ciprian-stingu/EpromProgrammer/gui/src/QtIcons.h

/**
 * 
 * Eprom Programmer
 * 
 * Copyright (C) 2021-2023 Ciprian Stingu
 * ciprian stingu at gmail dot com
 * 
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
 */
//----------------------------------------------------------------------
#ifndef QT_ICON_H
#define QT_ICON_H
//----------------------------------------------------------------------
/* XPM */
const char *guiIcon[]={
"256 256 852 2",
"Qt c None",
"#D c #000001",
".j c #000101",
".w c #010101",
".# c #010102",
".O c #010102",
"#l c #010103",
".i c #010202",
"h6 c #010203",
".a c #010304",
"id c #020305",
"ll c #020306",
"ib c #020405",
"lr c #020406",
".b c #020406",
".P c #020407",
"#S c #020507",
"a. c #030507",
".c c #030508",
"kJ c #030608",
".h c #030609",
".d c #030609",
".e c #04070a",
".f c #04070b",
".g c #04080c",
"ic c #04090c",
"#R c #05090d",
".6 c #05090d",
"#E c #05090e",
"#k c #050a0e",
"jq c #050a0f",
".x c #050a10",
"la c #060a10",
"cp c #060b10",
"l# c #060b10",
".Q c #060b11",
"kY c #060b12",
"il c #060c11",
"a# c #060c12",
"#9 c #070d13",
"#T c #070d14",
"lq c #070e15",
".k c #080e15",
"kG c #080e16",
"ct c #080f16",
".N c #080f16",
"d3 c #080f17",
"dr c #081017",
".v c #091018",
".5 c #091119",
"at c #0a131b",
"cq c #0a131c",
"#m c #0a131d",
"#C c #0a141d",
"cu c #0b151f",
"cs c #0c1722",
"aN c #0c1722",
".7 c #0d1723",
"cr c #0d1823",
"h9 c #0d1924",
"cg c #0d1925",
"js c #0d1a25",
"lp c #0d1a26",
"i# c #0e1a26",
".R c #0e1a27",
".l c #0e1b27",
".u c #0e1b28",
"#U c #0e1b29",
"co c #0f1c29",
"jl c #0f1d2a",
"bk c #0f1d2b",
"jt c #101e2c",
"lb c #101e2d",
"bN c #101f2d",
".y c #101f2e",
"bX c #10202f",
"aa c #11202f",
".4 c #11202f",
"b3 c #112130",
"#Q c #112130",
"#F c #122131",
"cJ c #122231",
"h7 c #122232",
".M c #122232",
"hR c #122333",
".m c #122333",
"hW c #122334",
".t c #122434",
"hV c #142638",
"kH c #142739",
"hX c #15293b",
"lm c #15293c",
"kX c #16293c",
".n c #15293d",
".8 c #16293d",
"hU c #162a3e",
"hH c #172b3f",
"hS c #172c40",
"hT c #172d42",
"lo c #182d42",
".o c #182e43",
"im c #193046",
"ln c #193147",
"au c #1a3147",
"ih c #1a3148",
".p c #1a3149",
"#n c #1a314a",
"cv c #1a3249",
"l. c #1a334a",
".q c #1a334b",
"kZ c #1b324b",
"ii c #1b334b",
".S c #1b334c",
".r c #1b344c",
".s c #1b344c",
"kA c #1b344d",
"#8 c #1c344d",
"lk c #1b354e",
"#V c #1c354e",
"ab c #1c354e",
".z c #1c364e",
"ig c #1c364f",
"if c #1c3650",
".L c #1d3852",
"kq c #1d3954",
"jo c #1e3954",
"kB c #1e3a55",
"jw c #1f3b57",
".9 c #1f3b57",
"jn c #1f3c57",
"kh c #1f3c58",
"a4 c #203c59",
"cK c #203d59",
"aO c #203d59",
"j9 c #203d5a",
"hy c #203e5b",
"jm c #213e5b",
"ek c #213f5c",
"it c #213f5d",
"#j c #21405d",
"d4 c #21405e",
"jj c #22415e",
"iu c #22415f",
"ho c #224260",
"ds c #234261",
"dK c #234362",
"ht c #234362",
"cQ c #244565",
"bj c #244565",
"lj c #244666",
"lc c #254666",
"a5 c #254667",
".A c #254767",
"cP c #254768",
".K c #254769",
"ij c #264869",
"cR c #26496a",
"cO c #26496b",
"#G c #26496c",
"#P c #264a6c",
"cN c #274b6e",
"j0 c #274c6e",
"bA c #274c6f",
"cL c #284c70",
"kz c #284c70",
"bl c #284d70",
"as c #284d71",
"k9 c #284e72",
"ac c #294d71",
"hI c #294e72",
".T c #294e72",
"cM c #294e73",
"av c #294f73",
"kQ c #294f75",
"ki c #295075",
"ch c #2a5075",
"#. c #295075",
"kr c #295076",
"bM c #295175",
".3 c #295176",
"#o c #2a5076",
"ia c #2a5176",
"i. c #2a5177",
"kK c #2a5277",
"bB c #2b5277",
"li c #2a5278",
"cb c #2b5278",
"ld c #2b5278",
"bW c #2b5378",
"#B c #2b5379",
".B c #2b5379",
".J c #2b537a",
"#i c #2b537a",
"bY c #2c547b",
"b9 c #2c547b",
"h8 c #2c557c",
"in c #2d567e",
"ju c #2d567e",
"ie c #2d577f",
"cS c #2e5881",
"jr c #2f5a83",
"kF c #2f5a85",
"#7 c #2f5b85",
"le c #2f5b85",
"#W c #305b85",
".C c #2f5b86",
".I c #2f5c87",
"hN c #305c87",
"cw c #305d88",
"hO c #315d89",
"kC c #305d89",
"hM c #315e89",
"kg c #315e8a",
"a3 c #325e8a",
"aP c #32608c",
"hL c #32618d",
"k8 c #32628f",
"lh c #33628e",
"hJ c #33628f",
"k0 c #33618f",
"lf c #33628f",
".D c #336290",
".U c #346390",
"kW c #336392",
".2 c #336492",
"aM c #346391",
"hY c #346492",
"aw c #346492",
"#p c #346493",
"## c #346493",
"kL c #346593",
"hK c #356593",
"kj c #346594",
"ir c #356594",
".E c #346595",
"lg c #346694",
"#h c #356695",
"iq c #356696",
"#A c #356797",
".F c #366797",
".G c #366797",
".H c #366898",
"ky c #366899",
"ad c #36699a",
"jx c #376a9b",
"ip c #386b9c",
"j8 c #376b9c",
"ks c #376b9d",
"bi c #376c9d",
"io c #386c9e",
"a6 c #396c9e",
"j1 c #396d9f",
"hz c #3a6fa2",
"#H c #3a6fa3",
"k7 c #3a70a3",
"#O c #3a70a4",
"#q c #3a70a4",
"kM c #3a70a5",
"el c #3b71a5",
".V c #3a71a5",
"hj c #3b71a5",
".1 c #3a72a6",
"kf c #3a71a6",
"#z c #3b71a6",
"jz c #3c72a7",
"d5 c #3c73a8",
"kV c #3a72a8",
"a2 c #3b72a8",
"kR c #3c72a8",
"aQ c #3c73a8",
"jk c #3c74a9",
"#a c #3c73a9",
"k. c #3c73aa",
"kp c #3b73aa",
"#g c #3b74aa",
"bz c #3c75aa",
"aL c #3c74ab",
"iv c #3d75ac",
"ax c #3c75ac",
"bm c #3e76ac",
"kk c #3c76ac",
"hp c #3e76ad",
"dt c #3e77ae",
"jy c #3e77af",
"d. c #3f78b0",
"kN c #3e78af",
"c9 c #3f79b0",
"#r c #3e78b0",
"c8 c #3f79b1",
"#y c #3e79b1",
"k6 c #407bb3",
"k1 c #3f7bb3",
".W c #407bb5",
"bL c #407cb4",
"is c #417cb5",
".0 c #407bb6",
"bC c #417cb6",
"#X c #417cb7",
"#6 c #417db7",
"j7 c #407db7",
"ke c #3f7db7",
"bh c #407db7",
"bV c #417eb8",
"kD c #417eb9",
"a1 c #407db8",
"bO c #427fba",
"k# c #407eb9",
"#b c #417eb9",
"#f c #417eba",
"a7 c #427fba",
"bZ c #437fbb",
"#s c #417eb9",
"#x c #417eba",
"b4 c #4380bb",
"c. c #4381bc",
"cx c #4381bd",
"ae c #4381be",
"c7 c #4482be",
"kt c #4381be",
"d# c #4482be",
"k5 c #4483be",
"hZ c #4483bf",
"ay c #4482bf",
"k2 c #4483bf",
"ik c #4483c0",
".X c #4483c1",
"kI c #4484c1",
"#I c #4583c1",
"jp c #4584c1",
"#N c #4484c2",
"cT c #4584c2",
"kO c #4282c0",
"jv c #4585c2",
"bg c #4282c0",
"#w c #4282c1",
"#t c #4382c1",
"hB c #4685c3",
"j2 c #4283c2",
"a8 c #4383c2",
"aR c #4484c3",
"hA c #4686c4",
"kU c #4484c3",
"hC c #4686c5",
"kS c #4385c3",
"by c #4486c3",
"da c #4687c5",
"dv c #4283c2",
"dQ c #4283c3",
"#c c #4484c4",
"a9 c #4485c4",
"du c #4686c5",
"k3 c #4687c5",
"k4 c #4787c5",
"#K c #4787c6",
"fD c #387dc0",
"fl c #397dc0",
"i0 c #397ec0",
"gL c #3a7ec1",
"e5 c #3b7fc1",
"fC c #3b7fc2",
"fk c #3b80c2",
"fu c #3b80c3",
"jg c #3c7fc1",
"iO c #3c80c1",
"jb c #3c80c2",
"fL c #3c80c3",
"d8 c #3c81c3",
"g0 c #3d80c2",
"d7 c #3d81c3",
"gw c #3d81c4",
"eM c #3e81c2",
"e4 c #3e81c3",
"jf c #3e82c3",
"dP c #3e82c4",
"ji c #3f82c2",
"dO c #3f82c4",
"d9 c #3f83c4",
"hc c #4082c3",
"f# c #4083c4",
"d6 c #4083c5",
"iP c #4084c5",
"#v c #4183c3",
"e6 c #4183c4",
"kP c #4184c3",
"jM c #4184c4",
"dN c #4184c5",
"bJ c #4284c3",
"#u c #4284c4",
"eL c #4284c5",
"jc c #4285c5",
"bn c #4384c4",
"bx c #4385c4",
"bo c #4385c5",
"e. c #4385c6",
"#d c #4485c5",
"kT c #4486c4",
"#e c #4486c5",
"dM c #4486c6",
"er c #4586c6",
"bK c #4587c5",
"bU c #4587c6",
"#M c #4687c6",
".Y c #4687c7",
"#L c #4688c7",
"#J c #4787c7",
".Z c #4788c7",
"ar c #4789c8",
"dL c #4888c7",
"af c #4888c8",
"eA c #4889c7",
"#Y c #4889c8",
"az c #4989c8",
"aK c #498ac8",
"#Z c #498ac9",
"em c #4a8ac8",
"ag c #4a8ac9",
"aq c #4a8bc9",
"jL c #4b8bc9",
"gZ c #4c8bc9",
"jA c #4c8cc9",
"#0 c #4c8cca",
"en c #4d8cc9",
"ko c #4d8dcb",
"ah c #4d8ecb",
"eq c #4e8dc9",
"jV c #4e8dca",
"bp c #4e8ecc",
"gK c #4f8dca",
"iZ c #4f8eca",
"bD c #4f8fcd",
"eo c #508eca",
"bP c #508fcd",
"#1 c #5090cd",
"ep c #518fca",
"hb c #518fcb",
"iw c #5290cb",
"jB c #5390cb",
"kd c #5392cf",
"aS c #5393cf",
"jE c #5491cc",
"ai c #5493cf",
"aA c #5494cf",
"iD c #5591cc",
"jh c #5592cc",
"#2 c #5593d0",
"jC c #5893cd",
"jD c #5894cd",
"#3 c #5896d2",
"g5 c #5994cd",
"eB c #5994ce",
"kE c #5997d3",
"#4 c #5a97d3",
"#5 c #5a98d4",
"ha c #5b96ce",
"b. c #5c9ad5",
"eK c #5d97cf",
"kn c #5d9bd6",
"aB c #5e9cd6",
"kc c #5e9cd7",
"aj c #5f9cd7",
"aT c #5f9dd7",
"gR c #6099d0",
"g6 c #6199d0",
"g9 c #619ad0",
"h# c #619ad1",
"h. c #629ad1",
"g8 c #629bd1",
"g7 c #639bd1",
"iE c #649cd1",
"bq c #65a1db",
"gY c #669ed2",
"jd c #679ed3",
"ix c #6aa0d4",
"bE c #6aa5de",
"kx c #6aa6df",
"eT c #6ba0d4",
"iA c #6ba1d4",
"ak c #6ba6df",
"bQ c #6ba7df",
"iC c #6ca1d4",
"iB c #6ca2d5",
"jZ c #6ca6df",
"aU c #6ca7df",
"b0 c #6ca7e0",
"iz c #6da2d5",
"b5 c #6da7e0",
"b8 c #6da8e0",
"km c #6da8e1",
"iy c #6ea2d5",
"jN c #6ea3d5",
"aC c #6ea9e1",
"b# c #6eaae1",
"eC c #6fa4d6",
"gx c #71a5d6",
"eJ c #73a6d7",
"ku c #73ade5",
"al c #74ade4",
"j# c #75a8d8",
"fV c #76a8d8",
"fa c #77a9d8",
"jF c #77a9d9",
"kv c #77b0e7",
"fM c #78a9d9",
"i9 c #78aad9",
"am c #78b0e7",
"kw c #78b1e8",
"fv c #79aad9",
"an c #79b1e8",
"ao c #79b2e8",
"ap c #79b2e9",
"gJ c #7babda",
"kb c #7bb3ea",
"ka c #7bb4ea",
"jK c #7cadda",
"aV c #7cb4ea",
"j6 c #7cb5eb",
"bf c #7db5eb",
"ba c #7db6eb",
"iY c #7eaedb",
"kl c #7fb7ec",
"eD c #80afdc",
"aD c #80b7ec",
"eH c #81b0dc",
"eG c #82b0dc",
"gc c #82b1dc",
"jY c #83b1dd",
"eI c #84b1dd",
"eF c #84b2dd",
"gq c #85b2dd",
"gj c #85b3dd",
"i1 c #85b3de",
"bI c #85bcf1",
"bF c #85bdf1",
"eE c #86b3de",
"iF c #88b4de",
"j5 c #88bef2",
"j3 c #88bff2",
"bb c #89bff2",
"bR c #89bff3",
"b1 c #8ac0f3",
"ca c #8ac0f4",
"b6 c #8ac1f4",
"c# c #8bc1f4",
"jG c #8cb7e0",
"aE c #8cc1f4",
"jJ c #8db8e0",
"bw c #8dc2f5",
"br c #8dc3f5",
"iN c #8eb9e1",
"je c #90bae1",
"jI c #91bae2",
"aF c #91c5f8",
"cm c #91c8fd",
"cl c #91c9fd",
"jH c #92bbe2",
"bc c #92c7f9",
"ck c #92c9fd",
"aG c #93c7f9",
"aH c #93c8fa",
"fE c #93c9fd",
"cj c #93cafd",
"aJ c #94c8fa",
"aI c #94c9fa",
"cn c #94cafd",
"ci c #95cafd",
"cf c #95cbfd",
"bv c #96cafc",
"bs c #96cbfc",
"ce c #96cbfd",
"eU c #97bfe4",
"aW c #97cafc",
"cd c #97cbfd",
"cc c #97ccfd",
"gS c #98bfe4",
"bt c #98ccfd",
"gV c #99c0e5",
"bd c #99ccfd",
"bH c #99cdfd",
"bu c #99cdfe",
"gX c #9ac1e5",
"dJ c #9acdfd",
"bT c #9acdfe",
"bS c #9acefe",
"bG c #9aceff",
"cy c #9bcdfd",
"dR c #9bcefd",
"b2 c #9bceff",
"b7 c #9bcfff",
"gW c #9cc2e6",
"cI c #9ccefd",
"aX c #9cceff",
"be c #9ccfff",
"j4 c #9cd0ff",
"gU c #9dc3e6",
"fF c #9dcefd",
"db c #9dcffd",
"aY c #9dd0ff",
"a0 c #9dd1ff",
"jO c #9ec4e7",
"es c #9ecffd",
"aZ c #9ed1ff",
"gT c #9fc4e7",
"e3 c #9fc5e7",
"cz c #9fcffd",
"ez c #9fd0fd",
"cH c #a0d0fd",
"cU c #a1d0fd",
"eN c #a1d1fd",
"cA c #a2d1fd",
"iG c #a3c7e8",
"dq c #a3d1fd",
"cG c #a3d2fd",
"gy c #a4c8e9",
"hi c #a4d2fd",
"iJ c #a5c8e9",
"cB c #a5d2fd",
"cF c #a5d3fd",
"iM c #a6c9e9",
"g1 c #a6d3fd",
"jU c #a7caea",
"cC c #a7d3fd",
"g4 c #a7d4fd",
"iK c #a8cbea",
"cD c #a8d4fd",
"iI c #a9cbeb",
"cE c #a9d4fd",
"et c #a9d5fd",
"iQ c #aacceb",
"dc c #aad5fd",
"iH c #abcdeb",
"h5 c #abd6fd",
"iL c #accdeb",
"d2 c #acd6fd",
"ey c #acd7fd",
"cV c #add6fd",
"hx c #add7fd",
"gI c #aecfec",
"eS c #aed7fd",
"h0 c #afd7fd",
"hq c #afd8fd",
"fW c #b0d0ed",
"hD c #b0d8fd",
"i7 c #b1d0ed",
"i5 c #b1d1ed",
"c6 c #b1d8fd",
"dp c #b1d9fd",
"fb c #b2d1ee",
"h1 c #b2d9fd",
"jW c #b3d2ee",
"dI c #b3d9fd",
"h4 c #b3d9fe",
"hd c #b3dafd",
"iX c #b4d3ee",
"fN c #b4d3ef",
"gr c #b4dafd",
"j. c #b5d3ef",
"e# c #b5dafd",
"h2 c #b5dafe",
"g2 c #b5dbfd",
"gm c #b6d4ef",
"hQ c #b6dbfd",
"fG c #b6dbfe",
"ge c #b7d5f0",
"ft c #b7dbfd",
"h3 c #b7dbfe",
"hu c #b7dcfd",
"fw c #b8d5f0",
"cW c #b8dcfd",
"gk c #b8dcfe",
"eV c #b9d6f0",
"gv c #b9dcfd",
"dS c #b9dcfe",
"hw c #b9ddfd",
"fR c #baddfe",
"ej c #badefe",
"eZ c #bbd7f1",
"eY c #bbd8f1",
"c5 c #bbddfd",
"i6 c #bcd8f1",
"dw c #bcdefd",
"gd c #bcdefe",
"e2 c #bdd9f2",
"dd c #bddefd",
"fK c #bddefe",
"fZ c #bddffe",
"jX c #bedaf2",
"eR c #bedffd",
"f7 c #bedffe",
"e0 c #bfdaf3",
"d1 c #bfdffe",
"cX c #c0e0fe",
"eX c #c1dbf3",
"gp c #c1dcf3",
"f. c #c1e0fd",
"fU c #c1e0fe",
"i4 c #c2dcf3",
"c4 c #c2e1fe",
"eW c #c3ddf4",
"dH c #c3e1fd",
"eu c #c3e1fe",
"do c #c3e2fd",
"e1 c #c4ddf4",
"f2 c #c4e2fe",
"jR c #c5def5",
"g. c #c5e2fe",
"jQ c #c6dff5",
"cY c #c6e3fe",
"jT c #c7e0f5",
"hs c #c7e3fe",
"gQ c #c7e4fe",
"c3 c #c8e3fe",
"ex c #c8e4fe",
"hv c #c9e4fe",
"jS c #cae2f6",
"dT c #cae4fe",
"jP c #cbe2f7",
"cZ c #cbe5fe",
"he c #cbe6fe",
"gz c #cce3f7",
"c2 c #cce5fe",
"hP c #cde6fe",
"gD c #cee4f8",
"gE c #cee5f8",
"c0 c #cee6fe",
"hh c #cee7fe",
"gC c #cfe5f8",
"c1 c #cfe7fe",
"gH c #d0e6f9",
"fs c #d0e8fe",
"ea c #d1e8fe",
"eO c #d2e8fe",
"gF c #d3e8fa",
"e9 c #d3e9fe",
"dn c #d3eafe",
"iR c #d4e8fa",
"gu c #d4eafe",
"gB c #d5e9fa",
"dG c #d5eafe",
"iV c #d6eafb",
"eQ c #d6ebfe",
"iU c #d7eafb",
"dU c #d7ebfe",
"ei c #d7ecfe",
"gA c #d8ebfb",
"gG c #d8ebfc",
"gM c #d8ecfe",
"gl c #d9ecfe",
"gP c #d9edfe",
"ja c #daecfc",
"hG c #daecfe",
"g3 c #daedfe",
"fJ c #dbedfe",
"de c #dcedfe",
"fX c #dceefd",
"d0 c #dceefe",
"fS c #ddeefe",
"iT c #ddeffd",
"dm c #deeffe",
"hn c #dfeffe",
"fc c #dff0fe",
"fm c #e0effe",
"dx c #e0f0fe",
"i8 c #e0f1fe",
"iS c #e0f1ff",
"e7 c #e1f0fe",
"iW c #e1f1ff",
"fg c #e1f2ff",
"ev c #e2f0fe",
"fT c #e2f1fe",
"f0 c #e2f1ff",
"ff c #e2f2ff",
"fr c #e3f1fe",
"f8 c #e3f2ff",
"fj c #e3f3ff",
"dV c #e4f1fe",
"dF c #e4f2fe",
"gb c #e4f3ff",
"df c #e5f2fe",
"f4 c #e5f2ff",
"f6 c #e5f3ff",
"fQ c #e5f4ff",
"gs c #e6f3fe",
"fP c #e6f4ff",
"f3 c #e6f5ff",
"dl c #e7f3fe",
"dZ c #e7f4fe",
"ew c #e7f4ff",
"fY c #e7f5ff",
"fh c #e7f6ff",
"eb c #e8f3ff",
"gN c #e8f4fe",
"hf c #e8f4ff",
"ga c #e8f6ff",
"gO c #e9f4fe",
"f9 c #e9f4ff",
"fe c #e9f7ff",
"gg c #eaf7ff",
"fA c #eaf8ff",
"f5 c #ebf5ff",
"fz c #ebf8ff",
"gi c #ebf9ff",
"fH c #ecf5fe",
"dg c #ecf5ff",
"eh c #ecf6ff",
"fd c #ecf9ff",
"dy c #edf6fe",
"dk c #edf6ff",
"fi c #edf9ff",
"g# c #edfaff",
"fn c #eef6fe",
"hr c #eef6ff",
"dW c #eef7fe",
"go c #eefaff",
"hF c #eff7ff",
"gh c #effbff",
"fq c #f0f7fe",
"dE c #f0f8fe",
"eP c #f0f8ff",
"i3 c #f0fbff",
"fO c #f0fcff",
"dh c #f1f7ff",
"dj c #f1f8ff",
"hk c #f1f9ff",
"fB c #f1fcff",
"di c #f2f8ff",
"e8 c #f2f9ff",
"fy c #f2fdff",
"ec c #f3f9ff",
"gn c #f3feff",
"hm c #f4f9ff",
"i2 c #f4feff",
"eg c #f5faff",
"gf c #f5ffff",
"hE c #f6faff",
"fx c #f6ffff",
"dz c #f7faff",
"dX c #f7fbff",
"fo c #f8fbff",
"dD c #f8fcff",
"fp c #f9fcff",
"ed c #fafcff",
"ef c #fafdff",
"gt c #fbfdff",
"f1 c #fbfeff",
"hl c #fcfdff",
"fI c #fcfeff",
"dY c #fdfeff",
"hg c #fdffff",
"dA c #fefeff",
"ee c #feffff",
"dC c #fffeff",
"dB c #ffffff",
"QtQtQtQtQtQtQtQtQtQtQtQtQtQtQtQtQtQtQtQtQtQtQtQtQtQtQtQtQtQtQtQtQtQtQtQtQtQtQtQtQtQtQtQtQtQtQtQtQtQtQtQtQtQtQtQtQtQtQtQtQtQtQtQtQtQtQtQtQtQtQtQtQtQtQtQtQtQtQtQtQtQtQtQtQtQtQtQtQtQtQtQtQtQtQtQtQtQtQtQtQtQtQtQtQtQtQtQtQtQtQtQtQtQtQtQtQtQtQtQtQtQtQtQtQtQtQtQtQtQtQtQtQtQtQtQtQtQtQtQtQtQtQtQtQtQtQtQtQtQtQtQtQtQtQtQtQtQtQtQtQtQtQtQtQtQtQtQtQtQtQtQtQtQtQtQtQtQtQtQtQtQtQtQtQtQtQtQtQtQtQtQtQtQtQtQtQtQtQtQtQtQtQtQtQtQtQtQtQtQtQtQtQtQtQtQtQtQtQtQtQtQtQtQtQtQtQtQtQtQtQtQtQtQtQtQtQtQtQtQtQtQtQtQtQtQtQtQtQtQtQtQtQtQtQtQt",
"QtQtQtQtQtQtQtQtQtQtQtQtQtQtQtQtQtQtQtQtQtQtQtQtQtQtQtQtQtQtQtQtQtQtQtQtQtQtQtQtQtQtQtQtQtQtQtQtQtQtQtQtQtQtQtQtQtQtQtQtQtQtQtQtQtQtQtQtQtQtQtQtQtQtQtQtQtQtQtQtQtQtQtQtQtQtQtQtQtQtQtQtQtQtQtQtQtQtQtQtQtQtQtQtQtQtQtQtQtQtQtQtQtQtQtQtQtQtQtQtQtQtQtQtQtQtQtQtQtQtQtQtQtQtQtQtQtQtQtQtQtQtQtQtQtQtQtQtQtQtQtQtQtQtQtQtQtQtQtQtQtQtQtQtQtQtQtQtQtQtQtQtQtQtQtQtQtQtQtQtQtQtQtQtQtQtQtQtQtQtQtQtQtQtQtQtQtQtQtQtQtQtQtQtQtQtQtQtQtQtQtQtQtQtQtQtQtQtQtQtQtQtQtQtQtQtQtQtQtQtQtQtQtQtQtQtQtQtQtQtQtQtQtQtQtQtQtQtQtQtQtQtQtQtQtQt",
"QtQtQtQtQtQtQtQtQtQtQtQtQtQtQtQtQtQtQtQtQtQtQtQtQtQtQtQtQtQtQtQtQtQtQtQtQtQtQtQtQtQtQtQtQtQtQtQtQtQtQtQtQtQtQtQtQtQtQtQtQtQtQtQtQtQtQtQtQtQtQtQtQtQtQtQtQtQtQtQtQtQtQtQtQtQtQtQtQtQtQtQtQtQtQtQtQtQtQtQtQtQtQtQtQtQtQtQtQtQtQtQtQtQtQtQtQtQtQtQtQtQtQtQtQtQtQtQtQtQtQtQtQtQtQtQtQtQtQtQtQtQtQtQtQtQtQtQtQtQtQtQtQtQtQtQtQtQtQtQtQtQtQtQtQtQtQtQtQtQtQtQtQtQtQtQtQtQtQtQtQtQtQtQtQtQtQtQtQtQtQtQtQtQtQtQtQtQtQtQtQtQtQtQtQtQtQtQtQtQtQtQtQtQtQtQtQtQtQtQtQtQtQtQtQtQtQtQtQtQtQtQtQtQtQtQtQtQtQtQtQtQtQtQtQtQtQtQtQtQtQtQtQtQtQtQt",
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
"QtQtQtQtQtQtQtQtQtQtQtQtQtQtQtQtQtQtQtQtQtQt.j.jQtQtQtQtQtQtQtQtQtQtQtQtQtQtQtQtQtQtQtQtQtQtQtQtQtQtcobBbZ#M#ubn#1b0cab7aZbGbtbtbtbtbtbtbtbtbtbtbtbtbtbtbtbtbtbtbtbtcccececfcicncncncncncicicfcecdccbtbtbtbtbtbtbtbtbtbtbtbtbtbtbtbtbtbtbtbtbtbtbtbtbtbtbtbtbtbtbtbtbtbtbtbtbtbtbtbtbtbtbtbtbtbtbtbtbtbtbtbtbtbtbtbtbtbtbtbtbtbtbtbtbtbtbtbtbtbtbtbtbtbtbtbtbtbtbtbtbtbtbtbtbtbtbtbtbtbtbtbtbtbtbtbtbGaZb7cab0#1bn#u#MbZbBcoQtQtQtQtQtQtQtQtQtQtQtQtQtQtQtQtQtQtQtQtQtQtQtQtQtQt.j.jQtQtQtQtQtQtQtQtQtQtQtQtQtQtQtQtQtQtQtQtQtQt",
"QtQtQtQtQtQtQtQtQtQtQtQtQtQtQtQtQtQtQtQtQtQtQtQt.acpcqcrcgcraNaNaNaNaNaNaNaNaNaNaNaNaNaNaNaNcsatctcucvcwcx#M#ubn#1b0cab7aZbGbtbtbtbtbtbtbtbtbtbtbtbtbtbtbtbtbtbtccbtcyczcAcBcCcDcEcEcEcDcCcFcGcHcIbHbtbtbtbtbtbtbtbtbtbtbtbtbtbtbtbtbtbtbtbtbtbtbtbtbtbtbtbtbtbtbtbtbtbtbtbtbtbtbtbtbtbtbtbtbtbtbtbtbtbtbtbtbtbtbtbtbtbtbtbtbtbtbtbtbtbtbtbtbtbtbtbtbtbtbtbtbtbtbtbtbtbtbtbtbtbtbtbtbtbtbtbtbtbtbtbtbGaZb7cab0#1bn#u#McxcwcvcuctatcsaNaNaNaNaNaNaNaNaNaNaNaNaNaNaNaNcrcgcrcqcp.aQtQtQtQtQtQtQtQtQtQtQtQtQtQtQtQtQtQtQtQtQtQtQtQt",
"QtQtQtQtQtQtQtQtQtQtQtQtQtQtQtQtQtQtQtQtQtQtQtQt.gcJcKcLcMcNcOcOcOcOcOcOcOcOcOcOcOcOcOcOcOcOcOcPcQcRcS#OcT#M#ubn#1b0cab7aZbGbtbtbtbtbtbtbtbtbtbtbtbtbtbtbtcccccecebtcUcVcWcXcYcZc0c1c0c2c3c4c5c6cBcIbtccccccccbtbtbtbtbtbtbtbtbtbtbtbtbtbtbtbtbtbtbtbtbtbtbtbtbtbtbtbtbtbtbtbtbtbtbtbtbtbtbtbtbtbtbtbtbtbtbtbtbtbtbtbtbtbtbtbtbtbtbtbtbtbtbtbtbtbtbtbtbtbtbtbtbtbtbtbtbtbtbtbtbtbtbtbtbtbtbtbtbtbtbtbGaZb7cab0#1bn#u#McT#OcScRcQcPcOcOcOcOcOcOcOcOcOcOcOcOcOcOcOcOcOcNcMcLcKcJ.gQtQtQtQtQtQtQtQtQtQtQtQtQtQtQtQtQtQtQtQtQtQtQtQt",
"QtQtQtQtQtQtQtQtQtQtQtQtQtQtQtQtQtQtQtQtQtQtQtQt#T.L#p#6c7bCc8c8c8c8c8c8c8c8c8c8c8c8c8c8c8c8c8c9d.c9bCd#dabUbJbn#1b0cab7aZbGbtbtbtbtbtbtbtbtbtbtbtbtbtbtcccdccccbtdbdcddc1dedfdgdhdidjdkdldmdndodpdqcIbdbtcdccbtbtbtbtbtbtbtbtbtbtbtbtbtbtbtbtbtbtbtbtbtbtbtbtbtbtbtbtbtbtbtbtbtbtbtbtbtbtbtbtbtbtbtbtbtbtbtbtbtbtbtbtbtbtbtbtbtbtbtbtbtbtbtbtbtbtbtbtbtbtbtbtbtbtbtbtbtbtbtbtbtbtbtbtbtbtbtbtbtbtbtbGaZb7cab0#1bnbJbUdad#bCc9d.c9c8c8c8c8c8c8c8c8c8c8c8c8c8c8c8c8c8bCc7#6#p.L#TQtQtQtQtQtQtQtQtQtQtQtQtQtQtQtQtQtQtQtQtQtQtQtQt",
"QtQtQtQtQtQtQtQtQtQtQtQtQtQtQtQtQtQtQtQtQtQtQtQtdrdsdt.Z.Z.Z.Z.Z.Y#MbUbU#M#M#M#M#M#M#M#M#M#M#MbUbUbU.Y#L.Zdudvbn#1b0cab7aZbGbtbtbtbtbtbtbtbtbtbtbtbtbtbtccccbHdbcGcVdwc1dxdydzdAdBdBdBdCdDdEdFdGdHdIcDcHdJcdcdbtbtbtbtbtbtbtbtbtbtbtbtbtbtbtbtbtbtbtbtbtbtbtbtbtbtbtbtbtbtbtbtbtbtbtbtbtbtbtbtbtbtbtbtbtbtbtbtbtbtbtbtbtbtbtbtbtbtbtbtbtbtbtbtbtbtbtbtbtbtbtbtbtbtbtbtbtbtbtbtbtbtbtbtbtbtbtbtbtbtbtbGaZb7cab0#1bndvdu.Z#L.YbUbUbU#M#M#M#M#M#M#M#M#M#M#MbUbU#M.Y.Z.Z.Z.Z.ZdtdsdrQtQtQtQtQtQtQtQtQtQtQtQtQtQtQtQtQtQtQtQtQtQtQtQt",
"QtQtQtQtQtQtQtQtQtQtQtQtQtQtQtQtQtQtQtQtQtQtQtQtdrdKd..Z.ZdL.ZdMdNdOdPdPdOdOdOdOdOdOdOdOdOdOdOdPdPdOdNdM#LdudQbn#1b0cab7aZbGbtbtbtbtbtbtbtbtbtbtbtbtbtbtcecedRcDdSdTdUdVdWdXdYdBdBdBdBdBdAdDdjdZd0c1d1d2dbcecebtbtbtbtbtbtbtbtbtbtbtbtbtbtbtbtbtbtbtbtbtbtbtbtbtbtbtbtbtbtbtbtbtbtbtbtbtbtbtbtbtbtbtbtbtbtbtbtbtbtbtbtbtbtbtbtbtbtbtbtbtbtbtbtbtbtbtbtbtbtbtbtbtbtbtbtbtbtbtbtbtbtbtbtbtbtbtbtbtbtbtbGaZb7cab0#1bndQdu#LdMdNdOdPdPdOdOdOdOdOdOdOdOdOdOdOdPdPdOdNdM.ZdL.Z.Zd.dKdrQtQtQtQtQtQtQtQtQtQtQtQtQtQtQtQtQtQtQtQtQtQtQtQt",
"QtQtQtQtQtQtQtQtQtQtQtQtQtQtQtQtQtQtQtQtQtQtQtQtd3d4d5.Z.ZdL.ZdMd6d7d8d7d7d7d7d7d7d7d7d7d7d7d7d7d8d7d9e.#L#M#ubn#1b0cab7aZbGbtbtbtbtbtbtbtbtbtbtbtbtbtbtcdcccHe#eaebecdXeddYeedBdBdBdBdBdBdYefdDegeheiejcAcccebtbtbtbtbtbtbtbtbtbtbtbtbtbtbtbtbtbtbtbtbtbtbtbtbtbtbtbtbtbtbtbtbtbtbtbtbtbtbtbtbtbtbtbtbtbtbtbtbtbtbtbtbtbtbtbtbtbtbtbtbtbtbtbtbtbtbtbtbtbtbtbtbtbtbtbtbtbtbtbtbtbtbtbtbtbtbtbtbtbtbtbGaZb7cab0#1bn#u#M#Le.d9d7d8d7d7d7d7d7d7d7d7d7d7d7d7d7d8d7d6dM.ZdL.Z.Zd5d4d3QtQtQtQtQtQtQtQtQtQtQtQtQtQtQtQtQtQtQtQtQtQtQtQt",
"QtQtQtQtQtQtQtQtQtQtQtQtQtQtQtQtQtQtQtQtQtQtQtQtctekel.Z.Z#L.ZemeneoepeoeoeoeoeoeoeoeoeoeoeoeoeoepeoeqemdLer#v#u#1b0cab7aZbGbtbtbtbtbtbtbtbtbtbtbtcccdbddJeseteueveddBdBdBdBdBdBdBdBdBdBdBdBdBdBdBdYewexeyezdJbdcccdbtbtbtbtbtbtbtbtbtbtbtbtbtbtbtbtbtbtbtbtbtbtbtbtbtbtbtbtbtbtbtbtbtbtbtbtbtbtbtbtbtbtbtbtbtbtbtbtbtbtbtbtbtbtbtbtbtbtbtbtbtbtbtbtbtbtbtbtbtbtbtbtbtbtbtbtbtbtbtbtbtbtbtbtbtbtbtbtbGaZb7cab0#1#u#verdLemeqeoepeoeoeoeoeoeoeoeoeoeoeoeoeoepeoenem.Z#L.Z.ZelekctQtQtQtQtQtQtQtQtQtQtQtQtQtQtQtQtQtQtQtQtQtQtQtQt",
"QtQtQtQtQtQtQtQtQtQtQtQtQtQtQtQtQtQtQtQtQtQtQtQtctekel.ZdMe.eAeBeCeDeEeFeGeHeHeHeHeHeHeHeHeHeHeIeEeGeJeKemeLeM#u#1b0cab7aZbGbtbtbtbtbtbtbtbtbtbtbtcecedJeNd2c5eOdgdBdBdBdBdBdBdBdBdBdBdBdBdBdBdBdBdBePeQeReScGcycececcbtbtbtbtbtbtbtbtbtbtbtbtbtbtbtbtbtbtbtbtbtbtbtbtbtbtbtbtbtbtbtbtbtbtbtbtbtbtbtbtbtbtbtbtbtbtbtbtbtbtbtbtbtbtbtbtbtbtbtbtbtbtbtbtbtbtbtbtbtbtbtbtbtbtbtbtbtbtbtbtbtbtbtbtbtbtbtbGaZb7cab0#1#ueMeLemeKeJeGeEeIeHeHeHeHeHeHeHeHeHeHeGeFeEeDeCeBeAe.dM.ZelekctQtQtQtQtQtQtQtQtQtQtQtQtQtQtQtQtQtQtQtQtQtQtQtQt",
"QtQtQtQtQtQtQtQtQtQtQtQtQtQtQtQtQtQtQtQtQtQtQtQtctekel.ZeLdOazeTeUeVeWeXeYeZeZeZeZeZeZeZeZeZeZe0e1e2e3eJeqe4e5e6#1b0cab7aZbGbtbtbtbtbtbtbtbtbtbtcccicncydcddc1e7e8dBdBdBdBdBdBdBdBdBdBdBdBdBdBdBdBdBegdfe9f.eSdbcfcnccbtbtbtbtbtbtbtbtbtbtbtbtbtbtbtbtbtbtbtbtbtbtbtbtbtbtbtbtbtbtbtbtbtbtbtbtbtbtbtbtbtbtbtbtbtbtbtbtbtbtbtbtbtbtbtbtbtbtbtbtbtbtbtbtbtbtbtbtbtbtbtbtbtbtbtbtbtbtbtbtbtbtbtbtbtbtbtbGaZb7cab0#1e6e5e4eqeJe3e2e1e0eZeZeZeZeZeZeZeZeZeZeYeXeWeVeUeTazdOeL.ZelekctQtQtQtQtQtQtQtQtQtQtQtQtQtQtQtQtQtQtQtQtQtQtQtQt",
"QtQtQtQtQtQtQtQtQtQtQtQtQtQtQtQtQtQtQtQtQtQtQtQtctekel#Lf#d8emfafbfcfdfefffgfgfgfgfgfgfgfgfgfgfhfifje2eGeofkfl#v#1b0cab7aZbGbtbtbtbtbtbtbtbtbtbtcccncjcIc6cZfmfnfodBdBdBdBdBdBdBdBdBdBdBdBdBdBdBdBdBfpfqfrfsftezcncjcdbtbtbtbtbtbtbtbtbtbtbtbtbtbtbtbtbtbtbtbtbtbtbtbtbtbtbtbtbtbtbtbtbtbtbtbtbtbtbtbtbtbtbtbtbtbtbtbtbtbtbtbtbtbtbtbtbtbtbtbtbtbtbtbtbtbtbtbtbtbtbtbtbtbtbtbtbtbtbtbtbtbtbtbtbtbtbtbGaZb7cab0#1#vflfkeoeGe2fjfifhfgfgfgfgfgfgfgfgfgfgfffefdfcfbfaemd8f##LelekctQtQtQtQtQtQtQtQtQtQtQtQtQtQtQtQtQtQtQtQtQtQtQtQt",
"QtQtQtQtQtQtQtQtQtQtQtQtQtQtQtQtQtQtQtQtQtQtQtQtctekel#Lf#fuemfvfwfhfxfyfzfAfAfAfAfAfAfAfAfAfAfBfxfie1eEepfCfD#v#1b0cab7aZbGbtbtbtbtbtbtbtbtbtbtcccjfEfFfGdGfHdXfIdBdBdBdBdBdBdBdBdBdBdBdBdBdBdBdBdBdYfodWfJfKcUcjfEcebtbtbtbtbtbtbtbtbtbtbtbtbtbtbtbtbtbtbtbtbtbtbtbtbtbtbtbtbtbtbtbtbtbtbtbtbtbtbtbtbtbtbtbtbtbtbtbtbtbtbtbtbtbtbtbtbtbtbtbtbtbtbtbtbtbtbtbtbtbtbtbtbtbtbtbtbtbtbtbtbtbtbtbtbtbtbtbGaZb7cab0#1#vfDfCepeEe1fifxfBfAfAfAfAfAfAfAfAfAfAfzfyfxfhfwfvemfuf##LelekctQtQtQtQtQtQtQtQtQtQtQtQtQtQtQtQtQtQtQtQtQtQtQtQt",
"QtQtQtQtQtQtQtQtQtQtQtQtQtQtQtQtQtQtQtQtQtQtQtQtctekel#Lf#fLemfMfNfffOfifPfQfQfQfQfQfQfQfQfQfQfzfBfhe0eIeofkfD#v#1b0cab7aZbGbtbtbtbtbtbtbtbtbtbtccfEckdbfRfSegeedBdBdBdBdBdBdBdBdBdBdBdBdBdBdBdBdBdBdBdAdXfTfUcAcjckcebtbtbtbtbtbtbtbtbtbtbtbtbtbtbtbtbtbtbtbtbtbtbtbtbtbtbtbtbtbtbtbtbtbtbtbtbtbtbtbtbtbtbtbtbtbtbtbtbtbtbtbtbtbtbtbtbtbtbtbtbtbtbtbtbtbtbtbtbtbtbtbtbtbtbtbtbtbtbtbtbtbtbtbtbtbtbtbGaZb7cab0#1#vfDfkeoeIe0fhfBfzfQfQfQfQfQfQfQfQfQfQfPfifOfffNfMemfLf##LelekctQtQtQtQtQtQtQtQtQtQtQtQtQtQtQtQtQtQtQtQtQtQtQtQt",
"QtQtQtQtQtQtQtQtQtQtQtQtQtQtQtQtQtQtQtQtQtQtQtQtctekel#Lf#d8emfVfWfXfAfYdxfcfcfcfcfcfcfcfcfcfcfQfAfgeZeHeofkfl#v#1b0cab7aZbGbtbtbtbtbtbtbtbtbtbtcdckclesfZf0f1dBdBdBdBdBdBdBdBdBdBdBdBdBdBdBdBdBdBdBdBdBdYebf2dqfEckcebtbtbtbtbtbtbtbtbtbtbtbtbtbtbtbtbtbtbtbtbtbtbtbtbtbtbtbtbtbtbtbtbtbtbtbtbtbtbtbtbtbtbtbtbtbtbtbtbtbtbtbtbtbtbtbtbtbtbtbtbtbtbtbtbtbtbtbtbtbtbtbtbtbtbtbtbtbtbtbtbtbtbtbtbtbtbtbGaZb7cab0#1#vflfkeoeHeZfgfAfQfcfcfcfcfcfcfcfcfcfcdxfYfAfXfWfVemd8f##LelekctQtQtQtQtQtQtQtQtQtQtQtQtQtQtQtQtQtQtQtQtQtQtQtQt",
"QtQtQtQtQtQtQtQtQtQtQtQtQtQtQtQtQtQtQtQtQtQtQtQtctekel#Lf#d8emfVfWfXfAf3dxfcfcfcfcfcfcfcfcfcfcfQfAfgeZeHeofkfl#v#1b0cab7aZbGbtbtbtbtbtbtbtbtbtbtcdckclesd1f4eedBdBdBdBdBdBdBdBdBdBdBdBdBdBdBdBdBdBdBdBdBdBf5cYdqckclcebtbtbtbtbtbtbtbtbtbtbtbtbtbtbtbtbtbtbtbtbtbtbtbtbtbtbtbtbtbtbtbtbtbtbtbtbtbtbtbtbtbtbtbtbtbtbtbtbtbtbtbtbtbtbtbtbtbtbtbtbtbtbtbtbtbtbtbtbtbtbtbtbtbtbtbtbtbtbtbtbtbtbtbtbtbtbtbGaZb7cab0#1#vflfkeoeHeZfgfAfQfcfcfcfcfcfcfcfcfcfcdxf3fAfXfWfVemd8f##LelekctQtQtQtQtQtQtQtQtQtQtQtQtQtQtQtQtQtQtQtQtQtQtQtQt",
"QtQtQtQtQtQtQtQtQtQtQtQtQtQtQtQtQtQtQtQtQtQtQtQtctekel#Lf#d8emfVfWfXfAf3dxfcfcfcfcfcfcfcfcfcfcfQfAfgeZeHeofkfl#v#1b0cab7aZbGbtbtbtbtbtbtbtbtbtbtcdckclesd1f6dBdBdBdBdBdBdBdBdBdBdBdBdBdBdBdBdBdBdBdBdBdBdBf5cYdqckclcebtbtbtbtbtbtbtbtbtbtbtbtbtbtbtbtbtbtbtbtbtbtbtbtbtbtbtbtbtbtbtbtbtbtbtbtbtbtbtbtbtbtbtbtbtbtbtbtbtbtbtbtbtbtbtbtbtbtbtbtbtbtbtbtbtbtbtbtbtbtbtbtbtbtbtbtbtbtbtbtbtbtbtbtbtbtbtbGaZb7cab0#1#vflfkeoeHeZfgfAfQfcfcfcfcfcfcfcfcfcfcdxf3fAfXfWfVemd8f##LelekctQtQtQtQtQtQtQtQtQtQtQtQtQtQtQtQtQtQtQtQtQtQtQtQt",
"QtQtQtQtQtQtQtQtQtQtQtQtQtQtQtQtQtQtQtQtQtQtQtQtctekel#Lf#d8emfVfWfXfAf3dxfcfcfcfcfcfcfcfcfcfcfQfAfgeZeHeofkfl#v#1b0cab7aZbGbtbtbtbtbtbtbtbtbtbtcdckclesf7f8dYdBdBdBdBdBdBdBdBdBdBdBdBdBdBdBdBdBdBdBdBdBeef9g.dqfEckcebtbtbtbtbtbtbtbtbtbtbtbtbtbtbtbtbtbtbtbtbtbtbtbtbtbtbtbtbtbtbtbtbtbtbtbtbtbtbtbtbtbtbtbtbtbtbtbtbtbtbtbtbtbtbtbtbtbtbtbtbtbtbtbtbtbtbtbtbtbtbtbtbtbtbtbtbtbtbtbtbtbtbtbtbtbtbtbGaZb7cab0#1#vflfkeoeHeZfgfAfQfcfcfcfcfcfcfcfcfcfcdxf3fAfXfWfVemd8f##LelekctQtQtQtQtQtQtQtQtQtQtQtQtQtQtQtQtQtQtQtQtQtQtQtQt",
"QtQtQtQtQtQtQtQtQtQtQtQtQtQtQtQtQtQtQtQtQtQtQtQtctekel#Lf#d8emfafbfcg#feffffffffffffffffffffffgag#gbe2gceofkfl#v#1b0cab7aZbGbtbtbtbtbtbtbtbtbtbtccfEckesgdfcdDdBdBdBdBdBdBdBdBdBdBdBdBdBdBdBdBdBdBdBdBdBfpf4c4cAfEckcebtbtbtbtbtbtbtbtbtbtbtbtbtbtbtbtbtbtbtbtbtbtbtbtbtbtbtbtbtbtbtbtbtbtbtbtbtbtbtbtbtbtbtbtbtbtbtbtbtbtbtbtbtbtbtbtbtbtbtbtbtbtbtbtbtbtbtbtbtbtbtbtbtbtbtbtbtbtbtbtbtbtbtbtbtbtbtbGaZb7cab0#1#vflfkeogce2gbg#gafffffffffffffffffffffffeg#fcfbfaemd8f##LelekctQtQtQtQtQtQtQtQtQtQtQtQtQtQtQtQtQtQtQtQtQtQtQtQt",
"QtQtQtQtQtQtQtQtQtQtQtQtQtQtQtQtQtQtQtQtQtQtQtQtctekel#Lf#fLemfvgef3gffBggfefefefefefefefefefeghgfgieWgjepfCfD#v#1b0cab7aZbGbtbtbtbtbtbtbtbtbtbtccfEckdbgkglePefdAdBdBdBdBdBdBdBdBdBdBdBdBdBdBdBdBdBdAefdifSf7eNcjckcebtbtbtbtbtbtbtbtbtbtbtbtbtbtbtbtbtbtbtbtbtbtbtbtbtbtbtbtbtbtbtbtbtbtbtbtbtbtbtbtbtbtbtbtbtbtbtbtbtbtbtbtbtbtbtbtbtbtbtbtbtbtbtbtbtbtbtbtbtbtbtbtbtbtbtbtbtbtbtbtbtbtbtbtbtbtbtbGaZb7cab0#1#vfDfCepgjeWgigfghfefefefefefefefefefeggfBgff3gefvemfLf##LelekctQtQtQtQtQtQtQtQtQtQtQtQtQtQtQtQtQtQtQtQtQtQtQtQt",
"QtQtQtQtQtQtQtQtQtQtQtQtQtQtQtQtQtQtQtQtQtQtQtQtctekel#Lf#fLemfvgmfQgnghgafhfhfhfhfhfhfhfhfhgagogngggpgqepfCfD#v#1b0cab7aZbGbtbtbtbtbtbtbtbtbtbtcccnfEcIgrfsgse8efdBdBdBdBdBdBdBdBdBdBdBdBdBdBdBdBdBgtecdlgugvcHcncjcdbtbtbtbtbtbtbtbtbtbtbtbtbtbtbtbtbtbtbtbtbtbtbtbtbtbtbtbtbtbtbtbtbtbtbtbtbtbtbtbtbtbtbtbtbtbtbtbtbtbtbtbtbtbtbtbtbtbtbtbtbtbtbtbtbtbtbtbtbtbtbtbtbtbtbtbtbtbtbtbtbtbtbtbtbtbtbtbGaZb7cab0#1#vfDfCepgqgpgggngogafhfhfhfhfhfhfhfhfhgaghgnfQgmfvemfLf##LelekctQtQtQtQtQtQtQtQtQtQtQtQtQtQtQtQtQtQtQtQtQtQtQtQt",
"QtQtQtQtQtQtQtQtQtQtQtQtQtQtQtQtQtQtQtQtQtQtQtQtctekel#LdNgwaKgxgygzgAgBgCgDgDgDgDgDgDgDgDgDgEgFgGgHgIgJgKd8gL#v#1b0cab7aZbGbtbtbtbtbtbtbtbtbtbtcccncncIeSg.gMgNegeedBdBdBdBdBdBdBdBdBdBdBdBdBdBdBdBdXgOgPgQdpescicncdbtbtbtbtbtbtbtbtbtbtbtbtbtbtbtbtbtbtbtbtbtbtbtbtbtbtbtbtbtbtbtbtbtbtbtbtbtbtbtbtbtbtbtbtbtbtbtbtbtbtbtbtbtbtbtbtbtbtbtbtbtbtbtbtbtbtbtbtbtbtbtbtbtbtbtbtbtbtbtbtbtbtbtbtbtbtbtbGaZb7cab0#1#vgLd8gKgJgIgHgGgFgEgDgDgDgDgDgDgDgDgDgCgBgAgzgygxaKgwdN#LelekctQtQtQtQtQtQtQtQtQtQtQtQtQtQtQtQtQtQtQtQtQtQtQtQt",
"QtQtQtQtQtQtQtQtQtQtQtQtQtQtQtQtQtQtQtQtQtQtQtQtctekel.Ze.dN#YgReDgSgTgUgVgVgVgVgVgVgVgVgVgVgVgWgTgXeEgYgZf#g0#u#1b0cab7aZbGbtbtbtbtbtbtbtbtbtbtbtcfcfdJg1g2cYg3ePdBdBdBdBdBdBdBdBdBdBdBdBdBdBdBdBdBecd0cYg2g4cIcecfccbtbtbtbtbtbtbtbtbtbtbtbtbtbtbtbtbtbtbtbtbtbtbtbtbtbtbtbtbtbtbtbtbtbtbtbtbtbtbtbtbtbtbtbtbtbtbtbtbtbtbtbtbtbtbtbtbtbtbtbtbtbtbtbtbtbtbtbtbtbtbtbtbtbtbtbtbtbtbtbtbtbtbtbtbtbtbtbGaZb7cab0#1#ug0f#gZgYeEgXgTgWgVgVgVgVgVgVgVgVgVgVgVgUgTgSeDgR#YdNe..ZelekctQtQtQtQtQtQtQtQtQtQtQtQtQtQtQtQtQtQtQtQtQtQtQtQt",
"QtQtQtQtQtQtQtQtQtQtQtQtQtQtQtQtQtQtQtQtQtQtQtQtctekel.Z.YbU.ZgKg5g6g7g8g9g9g9g9g9g9g9g9g9g9g9h.g7h#hahbaz#ehc#u#1b0cab7aZbGbtbtbtbtbtbtbtbtbtbtbtcecebHesg1hdhehfhgdBdBdBdBdBdBdBdBdBdBdBdBdBdBdBdBdghhhdhidbbHcdcdbtbtbtbtbtbtbtbtbtbtbtbtbtbtbtbtbtbtbtbtbtbtbtbtbtbtbtbtbtbtbtbtbtbtbtbtbtbtbtbtbtbtbtbtbtbtbtbtbtbtbtbtbtbtbtbtbtbtbtbtbtbtbtbtbtbtbtbtbtbtbtbtbtbtbtbtbtbtbtbtbtbtbtbtbtbtbtbtbGaZb7cab0#1#uhc#eazhbhah#g7h.g9g9g9g9g9g9g9g9g9g9g9g8g7g6g5gK.ZbU.Y.ZelekctQtQtQtQtQtQtQtQtQtQtQtQtQtQtQtQtQtQtQtQtQtQtQtQt",
"QtQtQtQtQtQtQtQtQtQtQtQtQtQtQtQtQtQtQtQtQtQtQtQtctekhj.Z.Z.Z.ZbUe.dNdNdNdNdNdNdNdNdNdNdNdNdNdNdNdNdNboer.Z#M#ubn#1b0cab7aZbGbtbtbtbtbtbtbtbtbtbtbtccccbtbHcIg1f7fJhkgtdYdYeedBdBdBdBdBdBdBeedYdYhlhmhncXcFbHccbtbtccbtbtbtbtbtbtbtbtbtbtbtbtbtbtbtbtbtbtbtbtbtbtbtbtbtbtbtbtbtbtbtbtbtbtbtbtbtbtbtbtbtbtbtbtbtbtbtbtbtbtbtbtbtbtbtbtbtbtbtbtbtbtbtbtbtbtbtbtbtbtbtbtbtbtbtbtbtbtbtbtbtbtbtbtbtbtbtbtbGaZb7cab0#1bn#u#M.ZerbodNdNdNdNdNdNdNdNdNdNdNdNdNdNdNdNdNe.bU.Z.Z.Z.ZhjekctQtQtQtQtQtQtQtQtQtQtQtQtQtQtQtQtQtQtQtQtQtQtQtQt",
"QtQtQtQtQtQtQtQtQtQtQtQtQtQtQtQtQtQtQtQtQtQtQtQtdrhohp.Z.ZeA.ZdMf#d7fLd8d7d7d7d7d7d7d7d7d7d7d7d8fLd8d9e.#LdudQbn#1b0cab7aZbGbtbtbtbtbtbtbtbtbtbtbtbtbtbtccbtezhqf2eQfrehecfpdAdBdBdBdBdBeeefeghrdfglhsc6escecebtbtbtbtbtbtbtbtbtbtbtbtbtbtbtbtbtbtbtbtbtbtbtbtbtbtbtbtbtbtbtbtbtbtbtbtbtbtbtbtbtbtbtbtbtbtbtbtbtbtbtbtbtbtbtbtbtbtbtbtbtbtbtbtbtbtbtbtbtbtbtbtbtbtbtbtbtbtbtbtbtbtbtbtbtbtbtbtbtbtbtbGaZb7cab0#1bndQdu#Le.d9d8fLd8d7d7d7d7d7d7d7d7d7d7d7d8fLd7f#dM.ZeA.Z.ZhphodrQtQtQtQtQtQtQtQtQtQtQtQtQtQtQtQtQtQtQtQtQtQtQtQt",
"QtQtQtQtQtQtQtQtQtQtQtQtQtQtQtQtQtQtQtQtQtQtQtQtdrhtc8.Z.Z.Z.Z.YdMe.boboe.e.e.e.e.e.e.e.e.e.e.boboe.dMbU.ZdudQbn#1b0cab7aZbGbtbtbtbtbtbtbtbtbtbtbtbtbtbtccbtcycAd2hucYdUgsdjeddBdBdBdBdBgtecgOg3hvhwhxcAcycdcdbtbtbtbtbtbtbtbtbtbtbtbtbtbtbtbtbtbtbtbtbtbtbtbtbtbtbtbtbtbtbtbtbtbtbtbtbtbtbtbtbtbtbtbtbtbtbtbtbtbtbtbtbtbtbtbtbtbtbtbtbtbtbtbtbtbtbtbtbtbtbtbtbtbtbtbtbtbtbtbtbtbtbtbtbtbtbtbtbtbtbtbGaZb7cab0#1bndQdu.ZbUdMe.boboe.e.e.e.e.e.e.e.e.e.e.boboe.dM.Y.Z.Z.Z.Zc8htdrQtQtQtQtQtQtQtQtQtQtQtQtQtQtQtQtQtQtQtQtQtQtQtQt",
"QtQtQtQtQtQtQtQtQtQtQtQtQtQtQtQtQtQtQtQtQtQtQtQtcthyhz.Z.Z.ZhAhAhAhAhAhAhAhAhAhAhAhAhAhAhAhAhAhBhBhAhCda.ZbUbJ#u#1b0cab7aZbGbtbtbtbtbtbtbtbtbtbtbtbtbtbtccccbtbddRcAhDf2dUdVhregfpgtedhEhFgshGexhdcGdRbHbtccccbtbtbtbtbtbtbtbtbtbtbtbtbtbtbtbtbtbtbtbtbtbtbtbtbtbtbtbtbtbtbtbtbtbtbtbtbtbtbtbtbtbtbtbtbtbtbtbtbtbtbtbtbtbtbtbtbtbtbtbtbtbtbtbtbtbtbtbtbtbtbtbtbtbtbtbtbtbtbtbtbtbtbtbtbtbtbtbtbtbtbtbGaZb7cab0#1#ubJbU.ZdahChAhBhBhAhAhAhAhAhAhAhAhAhAhAhAhAhAhAhAhA.Z.Z.ZhzhyctQtQtQtQtQtQtQtQtQtQtQtQtQtQtQtQtQtQtQtQtQtQtQtQt",
"QtQtQtQtQtQtQtQtQtQtQtQtQtQtQtQtQtQtQtQtQtQtQtQtcphHhIhJhKhLhMhMhMhMhMhMhMhMhMhMhMhMhMhMhMhMhMhN#WhO.Hd.hB#MbJbn#1b0cab7aZbGbtbtbtbtbtbtbtbtbtbtbtbtbtbtcccdcdcecebHhidIc4c2e9gld0fSd0hGdGhPf2hQg1dJcececcccbtbtbtbtbtbtbtbtbtbtbtbtbtbtbtbtbtbtbtbtbtbtbtbtbtbtbtbtbtbtbtbtbtbtbtbtbtbtbtbtbtbtbtbtbtbtbtbtbtbtbtbtbtbtbtbtbtbtbtbtbtbtbtbtbtbtbtbtbtbtbtbtbtbtbtbtbtbtbtbtbtbtbtbtbtbtbtbtbtbtbtbtbGaZb7cab0#1bnbJ#MhBd..HhO#WhNhMhMhMhMhMhMhMhMhMhMhMhMhMhMhMhMhMhLhKhJhIhHcpQtQtQtQtQtQtQtQtQtQtQtQtQtQtQtQtQtQtQtQtQtQtQtQt",
"QtQtQtQtQtQtQtQtQtQtQtQtQtQtQtQtQtQtQtQtQtQtQtQta.cqhRhShThHhUhUhUhUhUhUhUhUhUhUhUhUhUhUhUhUhUhVhWhXd4hYhZ#M#ubn#1b0cab7aZbGbtbtbtbtbtbtbtbtbtbtbtbtbtbtbtcccccdcdbtfFhidch0h1h2fGh3h3h2h4hDh5cFesbtcdcdbtbtbtbtbtbtbtbtbtbtbtbtbtbtbtbtbtbtbtbtbtbtbtbtbtbtbtbtbtbtbtbtbtbtbtbtbtbtbtbtbtbtbtbtbtbtbtbtbtbtbtbtbtbtbtbtbtbtbtbtbtbtbtbtbtbtbtbtbtbtbtbtbtbtbtbtbtbtbtbtbtbtbtbtbtbtbtbtbtbtbtbtbtbtbGaZb7cab0#1bn#u#MhZhYd4hXhWhVhUhUhUhUhUhUhUhUhUhUhUhUhUhUhUhUhUhHhThShRcqa.QtQtQtQtQtQtQtQtQtQtQtQtQtQtQtQtQtQtQtQtQtQtQtQt",
"QtQtQtQtQtQtQtQtQtQtQtQtQtQtQtQtQtQtQtQtQtQtQtQtQt.#h6.a.ah6h6h6h6h6h6h6h6h6h6h6h6h6h6h6h6h6h6QtQt.jh7h8b4#M#ubn#1b0cab7aZbGbtbtbtbtbtbtbtbtbtbtbtbtbtbtbtbtbtbtbtbtbtbdbHbHbHdJdJdJdJdJdJbHbHbdbtbtbtbtbtbtbtbtbtbtbtbtbtbtbtbtbtbtbtbtbtbtbtbtbtbtbtbtbtbtbtbtbtbtbtbtbtbtbtbtbtbtbtbtbtbtbtbtbtbtbtbtbtbtbtbtbtbtbtbtbtbtbtbtbtbtbtbtbtbtbtbtbtbtbtbtbtbtbtbtbtbtbtbtbtbtbtbtbtbtbtbtbtbtbtbtbtbtbGaZb7cab0#1bn#u#Mb4h8h7.jQtQth6h6h6h6h6h6h6h6h6h6h6h6h6h6h6h6h6h6.a.ah6.#QtQtQtQtQtQtQtQtQtQtQtQtQtQtQtQtQtQtQtQtQtQtQtQtQt",
"QtQtQtQtQtQtQtQtQtQtQtQtQtQtQtQtQtQtQtQtQtQt.j.jQtQtQtQtQtQtQtQtQtQtQtQtQtQtQtQtQtQtQtQtQtQtQtQtQtQth9chbZ#M#ubn#1b0cab7aZbGbtbtbtbtbtbtbtbtbtbtbtbtbtbtbtbtbtbtbtcccecicjckckclcmcmcmclckckcjcnceccbtbtbtbtbtbtbtbtbtbtbtbtbtbtbtbtbtbtbtbtbtbtbtbtbtbtbtbtbtbtbtbtbtbtbtbtbtbtbtbtbtbtbtbtbtbtbtbtbtbtbtbtbtbtbtbtbtbtbtbtbtbtbtbtbtbtbtbtbtbtbtbtbtbtbtbtbtbtbtbtbtbtbtbtbtbtbtbtbtbtbtbtbtbtbtbtbGaZb7cab0#1bn#u#MbZchh9QtQtQtQtQtQtQtQtQtQtQtQtQtQtQtQtQtQtQtQtQtQtQtQtQtQt.j.jQtQtQtQtQtQtQtQtQtQtQtQtQtQtQtQtQtQtQtQtQtQt",
"QtQtQtQtQtQtQtQtQtQtQtQtQtQtQtQtQtQtQtQtQtQt.j.jQtQtQtQtQtQtQtQtQtQtQtQtQtQtQtQtQtQtQtQtQtQtQtQtQtQt.ui.bZ#M#ubn#1b0cab7aZbGbtbtbtbtbtbtbtbtbtbtbtbtbtbtbtbtbtbtbtcccdcecicncncjcjcjcjcjcncncicecdccbtbtbtbtbtbtbtbtbtbtbtbtbtbtbtbtbtbtbtbtbtbtbtbtbtbtbtbtbtbtbtbtbtbtbtbtbtbtbtbtbtbtbtbtbtbtbtbtbtbtbtbtbtbtbtbtbtbtbtbtbtbtbtbtbtbtbtbtbtbtbtbtbtbtbtbtbtbtbtbtbtbtbtbtbtbtbtbtbtbtbtbtbtbtbtbtbGaZb7cab0#1bn#u#MbZi..uQtQtQtQtQtQtQtQtQtQtQtQtQtQtQtQtQtQtQtQtQtQtQtQtQtQt.j.jQtQtQtQtQtQtQtQtQtQtQtQtQtQtQtQtQtQtQtQtQtQt",
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
"QtQtQtQtQtQtQtQtQtQtQtQtQtQtQtQtQtQtQtQtQtQtQtQt.hcrhHif.Lig.s.s.s.s.s.s.s.s.s.s.s.s.s.s.s.s.sih.oiiij.Hik#M#ubn#1b0cab7aZbGbtbtbtbtbtbtbtbtbtbtbtbtbtbtbtbtbtbtbtbtbtbtbtbtbtbtbtbtbtbtbtbtbtbtbtbtbtbtbtbtbtbtbtbtbtbtbtbtbtbtbtbtbtbtbtbtbtbtbtbtbtbtbtbtbtbtbtbtbtbtbtbtbtbtbtbtbtbtbtbtbtbtbtbtbtbtbtbtbtbtbtbtbtbtbtbtbtbtbtbtbtbtbtbtbtbtbtbtbtbtbtbtbtbtbtbtbtbtbtbtbtbtbtbtbtbtbtbtbtbtbtbtbGaZb7cab0#1bn#u#Mik.Hijii.oih.s.s.s.s.s.s.s.s.s.s.s.s.s.s.s.s.sig.LifhHcr.hQtQtQtQtQtQtQtQtQtQtQtQtQtQtQtQtQtQtQtQtQtQtQtQt",
"QtQtQtQtQtQtQtQtQtQtQtQtQtQtQtQtQtQtQtQtQtQtQtQtiliminiohzip.H.H.H.H.H.H.H.H.H.H.H.H.H.H.H.H.Hiqir.G#HishA#MbJbn#1b0cab7aZbGbtbtbtbtbtbtbtbtbtbtbtbtbtbtbtbtbtbtbtbtbtbtbtbtbtbtbtbtbtbtbtbtbtbtbtbtbtbtbtbtbtbtbtbtbtbtbtbtbtbtbtbtbtbtbtbtbtbtbtbtbtbtbtbtbtbtbtbtbtbtbtbtbtbtbtbtbtbtbtbtbtbtbtbtbtbtbtbtbtbtbtbtbtbtbtbtbtbtbtbtbtbtbtbtbtbtbtbtbtbtbtbtbtbtbtbtbtbtbtbtbtbtbtbtbtbtbtbtbtbtbtbtbGaZb7cab0#1bnbJ#MhAis#H.Giriq.H.H.H.H.H.H.H.H.H.H.H.H.H.H.H.H.HiphzioinimilQtQtQtQtQtQtQtQtQtQtQtQtQtQtQtQtQtQtQtQtQtQtQtQt",
"QtQtQtQtQtQtQtQtQtQtQtQtQtQtQtQtQtQtQtQtQtQtQtQtd3itd5.Z.Z.Z.Z.Z.Z.Z.Z.Z.Z.Z.Z.Z.Z.Z.Z.Z.Z.Z.Z.Z.Z.Z.Z.Z.ZbUbJ#u#1b0cab7aZbGbtbtbtbtbtbtbtbtbtbtbtbtbtbtbtbtbtbtbtbtbtbtbtbtbtbtbtbtbtbtbtbtbtbtbtbtbtbtbtbtbtbtbtbtbtbtbtbtbtbtbtbtbtbtbtbtbtbtbtbtbtbtbtbtbtbtbtbtbtbtbtbtbtbtbtbtbtbtbtbtbtbtbtbtbtbtbtbtbtbtbtbtbtbtbtbtbtbtbtbtbtbtbtbtbtbtbtbtbtbtbtbtbtbtbtbtbtbtbtbtbtbtbtbtbtbtbtbtbtbtbtbtbGaZb7cab0#1#ubJbU.Z.Z.Z.Z.Z.Z.Z.Z.Z.Z.Z.Z.Z.Z.Z.Z.Z.Z.Z.Z.Z.Z.Z.Z.Z.Zd5itd3QtQtQtQtQtQtQtQtQtQtQtQtQtQtQtQtQtQtQtQtQtQtQtQt",
"QtQtQtQtQtQtQtQtQtQtQtQtQtQtQtQtQtQtQtQtQtQtQtQtdrhtc8.Z.Z.Z.ZbUe.eLdNdNdNeLeLeLeLeLeLeLeLeLeLdNdNdNboer.ZdudQbn#1b0cab7aZbGbtbtbtbtbtbtbtbtbtbtbtbtbtbtbtbtbtbtbtbtbtbtbtbtbtbtbtbtbtbtbtbtbtbtbtbtbtbtbtbtbtbtbtbtbtbtbtbtbtbtbtbtbtbtbtbtbtbtbtbtbtbtbtbtbtbtbtbtbtbtbtbtbtbtbtbtbtbtbtbtbtbtbtbtbtbtbtbtbtbtbtbtbtbtbtbtbtbtbtbtbtbtbtbtbtbtbtbtbtbtbtbtbtbtbtbtbtbtbtbtbtbtbtbtbtbtbtbtbtbtbtbtbGaZb7cab0#1bndQdu.ZerbodNdNdNeLeLeLeLeLeLeLeLeLeLdNdNdNeLe.bU.Z.Z.Z.Zc8htdrQtQtQtQtQtQtQtQtQtQtQtQtQtQtQtQtQtQtQtQtQtQtQtQt",
"QtQtQtQtQtQtQtQtQtQtQtQtQtQtQtQtQtQtQtQtQtQtQtQtd3iuiv.Z.ZeA.ZdMf#d8fufLd8d8d8d8d8d8d8d8d8d8d8fLfufLdObo#LdudQbn#1b0cab7aZbGbtbtbtbtbtbtbtbtbtbtbtbtbtbtbtbtbtbtbtbtbtbtbtbtbtbtbtbtbtbtbtbtbtbtbtbtbtbtbtbtbtbtbtbtbtbtbtbtbtbtbtbtbtbtbtbtbtbtbtbtbtbtbtbtbtbtbtbtbtbtbtbtbtbtbtbtbtbtbtbtbtbtbtbtbtbtbtbtbtbtbtbtbtbtbtbtbtbtbtbtbtbtbtbtbtbtbtbtbtbtbtbtbtbtbtbtbtbtbtbtbtbtbtbtbtbtbtbtbtbtbtbtbGaZb7cab0#1bndQdu#LbodOfLfufLd8d8d8d8d8d8d8d8d8d8d8fLfud8f#dM.ZeA.Z.Ziviud3QtQtQtQtQtQtQtQtQtQtQtQtQtQtQtQtQtQtQtQtQtQtQtQt",
"QtQtQtQtQtQtQtQtQtQtQtQtQtQtQtQtQtQtQtQtQtQtQtQtctekhj.Z.Z.Z.Z#LbUbUererererererererererererererererbU.Y.Z#MbJbn#1b0cab7aZbGbtbtbtbtbtbtbtbtbtbtbtbtbtbtbtbtbtbtbtbtbtbtbtbtbtbtbtbtbtbtbtbtbtbtbtbtbtbtbtbtbtbtbtbtbtbtbtbtbtbtbtbtbtbtbtbtbtbtbtbtbtbtbtbtbtbtbtbtbtbtbtbtbtbtbtbtbtbtbtbtbtbtbtbtbtbtbtbtbtbtbtbtbtbtbtbtbtbtbtbtbtbtbtbtbtbtbtbtbtbtbtbtbtbtbtbtbtbtbtbtbtbtbtbtbtbtbtbtbtbtbtbtbGaZb7cab0#1bnbJ#M.Z.YbUererererererererererererererererbUbU#L.Z.Z.Z.ZhjekctQtQtQtQtQtQtQtQtQtQtQtQtQtQtQtQtQtQtQtQtQtQtQtQt",
"QtQtQtQtQtQtQtQtQtQtQtQtQtQtQtQtQtQtQtQtQtQtQtQtctekel.ZbUdMdLiwgRixiyiziAiAiAiAiAiAiAiAiAiAiAiBiyiCg8iDazbohc#u#1b0cab7aZbGbtbtbtbtbtbtbtbtbtbtbtbtbtbtbtbtbtbtbtbtbtbtbtbtbtbtbtbtbtbtbtbtbtbtbtbtbtbtbtbtbtbtbtbtbtbtbtbtbtbtbtbtbtbtbtbtbtbtbtbtbtbtbtbtbtbtbtbtbtbtbtbtbtbtbtbtbtbtbtbtbtbtbtbtbtbtbtbtbtbtbtbtbtbtbtbtbtbtbtbtbtbtbtbtbtbtbtbtbtbtbtbtbtbtbtbtbtbtbtbtbtbtbtbtbtbtbtbtbtbtbtbtbGaZb7cab0#1#uhcboaziDg8iCiyiBiAiAiAiAiAiAiAiAiAiAiAiziyixgRiwdLdMbU.ZelekctQtQtQtQtQtQtQtQtQtQtQtQtQtQtQtQtQtQtQtQtQtQtQtQt",
"QtQtQtQtQtQtQtQtQtQtQtQtQtQtQtQtQtQtQtQtQtQtQtQtctekel.Zbod6aziEiFiGiHiIiJiJiJiJiJiJiJiJiJiJiJiKiLiMiNiAendOiO#u#1b0cab7aZbGbtbtbtbtbtbtbtbtbtbtbtbtbtbtbtbtbtbtbtbtbtbtbtbtbtbtbtbtbtbtbtbtbtbtbtbtbtbtbtbtbtbtbtbtbtbtbtbtbtbtbtbtbtbtbtbtbtbtbtbtbtbtbtbtbtbtbtbtbtbtbtbtbtbtbtbtbtbtbtbtbtbtbtbtbtbtbtbtbtbtbtbtbtbtbtbtbtbtbtbtbtbtbtbtbtbtbtbtbtbtbtbtbtbtbtbtbtbtbtbtbtbtbtbtbtbtbtbtbtbtbtbtbGaZb7cab0#1#uiOdOeniAiNiMiLiKiJiJiJiJiJiJiJiJiJiJiJiIiHiGiFiEazd6bo.ZelekctQtQtQtQtQtQtQtQtQtQtQtQtQtQtQtQtQtQtQtQtQtQtQtQt",
"QtQtQtQtQtQtQtQtQtQtQtQtQtQtQtQtQtQtQtQtQtQtQtQtctekel#LiPd7aKeJiQiRiSiTiUiViViViViViViViViViVfXiWgGiXiYiZfLi0#v#1b0cab7aZbGbtbtbtbtbtbtbtbtbtbtbtbtbtbtbtbtbtbtbtbtbtbtbtbtbtbtbtbtbtbtbtbtbtbtbtbtbtbtbtbtbtbtbtbtbtbtbtbtbtbtbtbtbtbtbtbtbtbtbtbtbtbtbtbtbtbtbtbtbtbtbtbtbtbtbtbtbtbtbtbtbtbtbtbtbtbtbtbtbtbtbtbtbtbtbtbtbtbtbtbtbtbtbtbtbtbtbtbtbtbtbtbtbtbtbtbtbtbtbtbtbtbtbtbtbtbtbtbtbtbtbtbtbGaZb7cab0#1#vi0fLiZiYiXgGiWfXiViViViViViViViViViViUiTiSiRiQeJaKd7iP#LelekctQtQtQtQtQtQtQtQtQtQtQtQtQtQtQtQtQtQtQtQtQtQtQtQt",
"QtQtQtQtQtQtQtQtQtQtQtQtQtQtQtQtQtQtQtQtQtQtQtQtctekel#Lf#fLemfvgef3gffBggfefefefefefefefefefeghgffdeWi1epfCfD#v#1b0cab7aZbGbtbtbtbtbtbtbtbtbtbtbtbtbtbtbtbtbtbtbtbtbtbtbtbtbtbtbtbtbtbtbtbtbtbtbtbtbtbtbtbtbtbtbtbtbtbtbtbtbtbtbtbtbtbtbtbtbtbtbtbtbtbtbtbtbtbtbtbtbtbtbtbtbtbtbtbtbtbtbtbtbtbtbtbtbtbtbtbtbtbtbtbtbtbtbtbtbtbtbtbtbtbtbtbtbtbtbtbtbtbtbtbtbtbtbtbtbtbtbtbtbtbtbtbtbtbtbtbtbtbtbtbtbGaZb7cab0#1#vfDfCepi1eWfdgfghfefefefefefefefefefeggfBgff3gefvemfLf##LelekctQtQtQtQtQtQtQtQtQtQtQtQtQtQtQtQtQtQtQtQtQtQtQtQt",
"QtQtQtQtQtQtQtQtQtQtQtQtQtQtQtQtQtQtQtQtQtQtQtQtctekel#Lf#fLemfvgmfQi2i3fegagagagagagagagagagagoi2fAi4gqepfCfD#v#1b0cab7aZbGbtbtbtbtbtbtbtbtbtbtbtbtbtbtbtbtbtbtbtbtbtbtbtbtbtbtbtbtbtbtbtbtbtbtbtbtbtbtbtbtbtbtbtbtbtbtbtbtbtbtbtbtbtbtbtbtbtbtbtbtbtbtbtbtbtbtbtbtbtbtbtbtbtbtbtbtbtbtbtbtbtbtbtbtbtbtbtbtbtbtbtbtbtbtbtbtbtbtbtbtbtbtbtbtbtbtbtbtbtbtbtbtbtbtbtbtbtbtbtbtbtbtbtbtbtbtbtbtbtbtbtbtbGaZb7cab0#1#vfDfCepgqi4fAi2gogagagagagagagagagagafei3i2fQgmfvemfLf##LelekctQtQtQtQtQtQtQtQtQtQtQtQtQtQtQtQtQtQtQtQtQtQtQtQt",
"QtQtQtQtQtQtQtQtQtQtQtQtQtQtQtQtQtQtQtQtQtQtQtQtctekel#Lf#d8emfVi5dmfdgaiWiWiWiWiWiWiWiWiWiWiWfYfdfji6eGeofkfl#v#1b0cab7aZbGbtbtbtbtbtbtbtbtbtbtbtbtbtbtbtbtbtbtbtbtbtbtbtbtbtbtbtbtbtbtbtbtbtbtbtbtbtbtbtbtbtbtbtbtbtbtbtbtbtbtbtbtbtbtbtbtbtbtbtbtbtbtbtbtbtbtbtbtbtbtbtbtbtbtbtbtbtbtbtbtbtbtbtbtbtbtbtbtbtbtbtbtbtbtbtbtbtbtbtbtbtbtbtbtbtbtbtbtbtbtbtbtbtbtbtbtbtbtbtbtbtbtbtbtbtbtbtbtbtbtbtbtbGaZb7cab0#1#vflfkeoeGi6fjfdfYiWiWiWiWiWiWiWiWiWiWiWgafddmi5fVemd8f##LelekctQtQtQtQtQtQtQtQtQtQtQtQtQtQtQtQtQtQtQtQtQtQtQtQt",
"QtQtQtQtQtQtQtQtQtQtQtQtQtQtQtQtQtQtQtQtQtQtQtQtctekel#Lf#d8emfVfWfXfAf3dxfcfcfcfcfcfcfcfcfcfcfQfAfgeZeHeofkfl#v#1b0cab7aZbGbtbtbtbtbtbtbtbtbtbtbtbtbtbtbtbtbtbtbtbtbtbtbtbtbtbtbtbtbtbtbtbtbtbtbtbtbtbtbtbtbtbtbtbtbtbtbtbtbtbtbtbtbtbtbtbtbtbtbtbtbtbtbtbtbtbtbtbtbtbtbtbtbtbtbtbtbtbtbtbtbtbtbtbtbtbtbtbtbtbtbtbtbtbtbtbtbtbtbtbtbtbtbtbtbtbtbtbtbtbtbtbtbtbtbtbtbtbtbtbtbtbtbtbtbtbtbtbtbtbtbtbtbGaZb7cab0#1#vflfkeoeHeZfgfAfQfcfcfcfcfcfcfcfcfcfcdxf3fAfXfWfVemd8f##LelekctQtQtQtQtQtQtQtQtQtQtQtQtQtQtQtQtQtQtQtQtQtQtQtQt",
"QtQtQtQtQtQtQtQtQtQtQtQtQtQtQtQtQtQtQtQtQtQtQtQtctekel#Lf#d8emfVfWfXfAf3dxfcfcfcfcfcfcfcfcfcfcfQfAfgeZeHeofkfl#v#1b0cab7aZbGbtbtbtbtbtbtbtbtbtbtbtbtbtbtbtbtbtbtbtbtbtbtbtbtbtbtbtbtbtbtbtbtbtbtbtbtbtbtbtbtbtbtbtbtbtbtbtbtbtbtbtbtbtbtbtbtbtbtbtbtbtbtbtbtbtbtbtbtbtbtbtbtbtbtbtbtbtbtbtbtbtbtbtbtbtbtbtbtbtbtbtbtbtbtbtbtbtbtbtbtbtbtbtbtbtbtbtbtbtbtbtbtbtbtbtbtbtbtbtbtbtbtbtbtbtbtbtbtbtbtbtbtbGaZb7cab0#1#vflfkeoeHeZfgfAfQfcfcfcfcfcfcfcfcfcfcdxf3fAfXfWfVemd8f##LelekctQtQtQtQtQtQtQtQtQtQtQtQtQtQtQtQtQtQtQtQtQtQtQtQt",
"QtQtQtQtQtQtQtQtQtQtQtQtQtQtQtQtQtQtQtQtQtQtQtQtctekel#Lf#d8emfVfWfXfAf3dxfcfcfcfcfcfcfcfcfcfcfQfAfgeZeHeofkfl#v#1b0cab7aZbGbtbtbtbtbtbtbtbtbtbtbtbtbtbtbtbtbtbtbtbtbtbtbtbtbtbtbtbtbtbtbtbtbtbtbtbtbtbtbtbtbtbtbtbtbtbtbtbtbtbtbtbtbtbtbtbtbtbtbtbtbtbtbtbtbtbtbtbtbtbtbtbtbtbtbtbtbtbtbtbtbtbtbtbtbtbtbtbtbtbtbtbtbtbtbtbtbtbtbtbtbtbtbtbtbtbtbtbtbtbtbtbtbtbtbtbtbtbtbtbtbtbtbtbtbtbtbtbtbtbtbtbtbGaZb7cab0#1#vflfkeoeHeZfgfAfQfcfcfcfcfcfcfcfcfcfcdxf3fAfXfWfVemd8f##LelekctQtQtQtQtQtQtQtQtQtQtQtQtQtQtQtQtQtQtQtQtQtQtQtQt",
"QtQtQtQtQtQtQtQtQtQtQtQtQtQtQtQtQtQtQtQtQtQtQtQtctekel#Lf#d8emfVi7iTfzfhi8dxdxdxdxdxdxdxdxdxdxfPfzffeYeGeofkfl#v#1b0cab7aZbGbtbtbtbtbtbtbtbtbtbtbtbtbtbtbtbtbtbtbtbtbtbtbtbtbtbtbtbtbtbtbtbtbtbtbtbtbtbtbtbtbtbtbtbtbtbtbtbtbtbtbtbtbtbtbtbtbtbtbtbtbtbtbtbtbtbtbtbtbtbtbtbtbtbtbtbtbtbtbtbtbtbtbtbtbtbtbtbtbtbtbtbtbtbtbtbtbtbtbtbtbtbtbtbtbtbtbtbtbtbtbtbtbtbtbtbtbtbtbtbtbtbtbtbtbtbtbtbtbtbtbtbtbGaZb7cab0#1#vflfkeoeGeYfffzfPdxdxdxdxdxdxdxdxdxdxi8fhfziTi7fVemd8f##LelekctQtQtQtQtQtQtQtQtQtQtQtQtQtQtQtQtQtQtQtQtQtQtQtQt",
"QtQtQtQtQtQtQtQtQtQtQtQtQtQtQtQtQtQtQtQtQtQtQtQtctekel#Lf#fLemi9j.gbfygofhf3f3f3f3f3f3f3f3f3fYfifyfeeXeFeofCfD#v#1b0cab7aZbGbtbtbtbtbtbtbtbtbtbtbtbtbtbtbtbtbtbtbtbtbtbtbtbtbtbtbtbtbtbtbtbtbtbtbtbtbtbtbtbtbtbtbtbtbtbtbtbtbtbtbtbtbtbtbtbtbtbtbtbtbtbtbtbtbtbtbtbtbtbtbtbtbtbtbtbtbtbtbtbtbtbtbtbtbtbtbtbtbtbtbtbtbtbtbtbtbtbtbtbtbtbtbtbtbtbtbtbtbtbtbtbtbtbtbtbtbtbtbtbtbtbtbtbtbtbtbtbtbtbtbtbtbGaZb7cab0#1#vfDfCeoeFeXfefyfifYf3f3f3f3f3f3f3f3f3fhgofygbj.i9emfLf##LelekctQtQtQtQtQtQtQtQtQtQtQtQtQtQtQtQtQtQtQtQtQtQtQtQt",
"QtQtQtQtQtQtQtQtQtQtQtQtQtQtQtQtQtQtQtQtQtQtQtQtctekel#Lf#fuemfvfwfhfxfyfzfAfAfAfAfAfAfAfAfAfAfOfxfdeWeEepfCfD#v#1b0cab7aZbGbtbtbtbtbtbtbtbtbtbtbtbtbtbtbtbtbtbtbtbtbtbtbtbtbtbtbtbtbtbtbtbtbtbtbtbtbtbtbtbtbtbtbtbtbtbtbtbtbtbtbtbtbtbtbtbtbtbtbtbtbtbtbtbtbtbtbtbtbtbtbtbtbtbtbtbtbtbtbtbtbtbtbtbtbtbtbtbtbtbtbtbtbtbtbtbtbtbtbtbtbtbtbtbtbtbtbtbtbtbtbtbtbtbtbtbtbtbtbtbtbtbtbtbtbtbtbtbtbtbtbtbtbGaZb7cab0#1#vfDfCepeEeWfdfxfOfAfAfAfAfAfAfAfAfAfAfzfyfxfhfwfvemfuf##LelekctQtQtQtQtQtQtQtQtQtQtQtQtQtQtQtQtQtQtQtQtQtQtQtQt",
"QtQtQtQtQtQtQtQtQtQtQtQtQtQtQtQtQtQtQtQtQtQtQtQtctekel#Ld6d8emj#gIjafhgbiTfXfXfXfXfXfXfXfXfXfXfffhfceVeDeojbi0#v#1b0cab7aZbGbtbtbtbtbtbtbtbtbtbtbtbtbtbtbtbtbtbtbtbtbtbtbtbtbtbtbtbtbtbtbtbtbtbtbtbtbtbtbtbtbtbtbtbtbtbtbtbtbtbtbtbtbtbtbtbtbtbtbtbtbtbtbtbtbtbtbtbtbtbtbtbtbtbtbtbtbtbtbtbtbtbtbtbtbtbtbtbtbtbtbtbtbtbtbtbtbtbtbtbtbtbtbtbtbtbtbtbtbtbtbtbtbtbtbtbtbtbtbtbtbtbtbtbtbtbtbtbtbtbtbtbtbGaZb7cab0#1#vi0jbeoeDeVfcfhfffXfXfXfXfXfXfXfXfXfXiTgbfhjagIj#emd8d6#LelekctQtQtQtQtQtQtQtQtQtQtQtQtQtQtQtQtQtQtQtQtQtQtQtQt",
"QtQtQtQtQtQtQtQtQtQtQtQtQtQtQtQtQtQtQtQtQtQtQtQtctekel.Zjcf#azjdjegIfwj.i7fWfWfWfWfWfWfWfWfWfWfNfwfbeUeCenjfjge6#1b0cab7aZbGbtbtbtbtbtbtbtbtbtbtbtbtbtbtbtbtbtbtbtbtbtbtbtbtbtbtbtbtbtbtbtbtbtbtbtbtbtbtbtbtbtbtbtbtbtbtbtbtbtbtbtbtbtbtbtbtbtbtbtbtbtbtbtbtbtbtbtbtbtbtbtbtbtbtbtbtbtbtbtbtbtbtbtbtbtbtbtbtbtbtbtbtbtbtbtbtbtbtbtbtbtbtbtbtbtbtbtbtbtbtbtbtbtbtbtbtbtbtbtbtbtbtbtbtbtbtbtbtbtbtbtbtbGaZb7cab0#1e6jgjfeneCeUfbfwfNfWfWfWfWfWfWfWfWfWfWi7j.fwgIjejdazf#jc.ZelekctQtQtQtQtQtQtQtQtQtQtQtQtQtQtQtQtQtQtQtQtQtQtQtQt",
"QtQtQtQtQtQtQtQtQtQtQtQtQtQtQtQtQtQtQtQtQtQtQtQtctekel.ZbUdMeAjhjdj#fvi9fVfVfVfVfVfVfVfVfVfVfVfMfvfaeTeBemjcji#u#1b0cab7aZbGbtbtbtbtbtbtbtbtbtbtbtbtbtbtbtbtbtbtbtbtbtbtbtbtbtbtbtbtbtbtbtbtbtbtbtbtbtbtbtbtbtbtbtbtbtbtbtbtbtbtbtbtbtbtbtbtbtbtbtbtbtbtbtbtbtbtbtbtbtbtbtbtbtbtbtbtbtbtbtbtbtbtbtbtbtbtbtbtbtbtbtbtbtbtbtbtbtbtbtbtbtbtbtbtbtbtbtbtbtbtbtbtbtbtbtbtbtbtbtbtbtbtbtbtbtbtbtbtbtbtbtbtbGaZb7cab0#1#ujijcemeBeTfafvfMfVfVfVfVfVfVfVfVfVfVfVi9fvj#jdjheAdMbU.ZelekctQtQtQtQtQtQtQtQtQtQtQtQtQtQtQtQtQtQtQtQtQtQtQtQt",
"QtQtQtQtQtQtQtQtQtQtQtQtQtQtQtQtQtQtQtQtQtQtQtQtctekel.Z.Z.Z.ZeAazemememememememememememememememememazeA.ZbU#v#u#1b0cab7aZbGbtbtbtbtbtbtbtbtbtbtbtbtbtbtbtbtbtbtbtbtbtbtbtbtbtbtbtbtbtbtbtbtbtbtbtbtbtbtbtbtbtbtbtbtbtbtbtbtbtbtbtbtbtbtbtbtbtbtbtbtbtbtbtbtbtbtbtbtbtbtbtbtbtbtbtbtbtbtbtbtbtbtbtbtbtbtbtbtbtbtbtbtbtbtbtbtbtbtbtbtbtbtbtbtbtbtbtbtbtbtbtbtbtbtbtbtbtbtbtbtbtbtbtbtbtbtbtbtbtbtbtbtbGaZb7cab0#1#u#vbU.ZeAazemememememememememememememememememazeA.Z.Z.Z.ZelekctQtQtQtQtQtQtQtQtQtQtQtQtQtQtQtQtQtQtQtQtQtQtQtQt",
"QtQtQtQtQtQtQtQtQtQtQtQtQtQtQtQtQtQtQtQtQtQtQtQtd3jjjk.Z.ZeA.ZdMf#d8fufLd8d8d8d8d8d8d8d8d8d8d8fLfud8dObo#L#M#ubn#1b0cab7aZbGbtbtbtbtbtbtbtbtbtbtbtbtbtbtbtbtbtbtbtbtbtbtbtbtbtbtbtbtbtbtbtbtbtbtbtbtbtbtbtbtbtbtbtbtbtbtbtbtbtbtbtbtbtbtbtbtbtbtbtbtbtbtbtbtbtbtbtbtbtbtbtbtbtbtbtbtbtbtbtbtbtbtbtbtbtbtbtbtbtbtbtbtbtbtbtbtbtbtbtbtbtbtbtbtbtbtbtbtbtbtbtbtbtbtbtbtbtbtbtbtbtbtbtbtbtbtbtbtbtbtbtbtbGaZb7cab0#1bn#u#M#LbodOd8fufLd8d8d8d8d8d8d8d8d8d8d8fLfud8f#dM.ZeA.Z.Zjkjjd3QtQtQtQtQtQtQtQtQtQtQtQtQtQtQtQtQtQtQtQtQtQtQtQt",
"QtQtQtQtQtQtQtQtQtQtQtQtQtQtQtQtQtQtQtQtQtQtQtQtdrhtc8.Z.Z.Z.ZbUjcd6f#f#f#f#f#f#f#f#f#f#f#f#f#f#f#f#eLdM.ZdudQbn#1b0cab7aZbGbtbtbtbtbtbtbtbtbtbtbtbtbtbtbtbtbtbtbtbtbtbtbtbtbtbtbtbtbtbtbtbtbtbtbtbtbtbtbtbtbtbtbtbtbtbtbtbtbtbtbtbtbtbtbtbtbtbtbtbtbtbtbtbtbtbtbtbtbtbtbtbtbtbtbtbtbtbtbtbtbtbtbtbtbtbtbtbtbtbtbtbtbtbtbtbtbtbtbtbtbtbtbtbtbtbtbtbtbtbtbtbtbtbtbtbtbtbtbtbtbtbtbtbtbtbtbtbtbtbtbtbtbGaZb7cab0#1bndQdu.ZdMeLf#f#f#f#f#f#f#f#f#f#f#f#f#f#f#f#d6jcbU.Z.Z.Z.Zc8htdrQtQtQtQtQtQtQtQtQtQtQtQtQtQtQtQtQtQtQtQtQtQtQtQt",
"QtQtQtQtQtQtQtQtQtQtQtQtQtQtQtQtQtQtQtQtQtQtQtQtd3iuiv.Z.Z.Z.Z.Z.Z#L#L#L#L#L#L#L#L#L#L#L#L#L#L#L#L#L.Z.Z.Zdudv#u#1b0cab7aZbGbtbtbtbtbtbtbtbtbtbtbtbtbtbtbtbtbtbtbtbtbtbtbtbtbtbtbtbtbtbtbtbtbtbtbtbtbtbtbtbtbtbtbtbtbtbtbtbtbtbtbtbtbtbtbtbtbtbtbtbtbtbtbtbtbtbtbtbtbtbtbtbtbtbtbtbtbtbtbtbtbtbtbtbtbtbtbtbtbtbtbtbtbtbtbtbtbtbtbtbtbtbtbtbtbtbtbtbtbtbtbtbtbtbtbtbtbtbtbtbtbtbtbtbtbtbtbtbtbtbtbtbtbGaZb7cab0#1#udvdu.Z.Z.Z#L#L#L#L#L#L#L#L#L#L#L#L#L#L#L#L#L.Z.Z.Z.Z.Z.Ziviud3QtQtQtQtQtQtQtQtQtQtQtQtQtQtQtQtQtQtQtQtQtQtQtQt",
"QtQtQtQtQtQtQtQtQtQtQtQtQtQtQtQtQtQtQtQtQtQtQtQta#.rhOivc8jkelelelelelelelelelelelelelelelelel#OhzelhpbOhC#MbJbn#1b0cab7aZbGbtbtbtbtbtbtbtbtbtbtbtbtbtbtbtbtbtbtbtbtbtbtbtbtbtbtbtbtbtbtbtbtbtbtbtbtbtbtbtbtbtbtbtbtbtbtbtbtbtbtbtbtbtbtbtbtbtbtbtbtbtbtbtbtbtbtbtbtbtbtbtbtbtbtbtbtbtbtbtbtbtbtbtbtbtbtbtbtbtbtbtbtbtbtbtbtbtbtbtbtbtbtbtbtbtbtbtbtbtbtbtbtbtbtbtbtbtbtbtbtbtbtbtbtbtbtbtbtbtbtbtbtbGaZb7cab0#1bnbJ#MhCbOhpelhz#Oeleleleleleleleleleleleleleleleleljkc8ivhO.ra#QtQtQtQtQtQtQtQtQtQtQtQtQtQtQtQtQtQtQtQtQtQtQtQt",
"QtQtQtQtQtQtQtQtQtQtQtQtQtQtQtQtQtQtQtQtQtQtQtQt.ejl.riuhtjjekekekekekekekekekekekekekekekekjmjnjohychiojp#M#ubn#1b0cab7aZbGbtbtbtbtbtbtbtbtbtbtbtbtbtbtbtbtbtbtbtbtbtbtbtbtbtbtbtbtbtbtbtbtbtbtbtbtbtbtbtbtbtbtbtbtbtbtbtbtbtbtbtbtbtbtbtbtbtbtbtbtbtbtbtbtbtbtbtbtbtbtbtbtbtbtbtbtbtbtbtbtbtbtbtbtbtbtbtbtbtbtbtbtbtbtbtbtbtbtbtbtbtbtbtbtbtbtbtbtbtbtbtbtbtbtbtbtbtbtbtbtbtbtbtbtbtbtbtbtbtbtbtbtbGaZb7cab0#1bn#u#Mjpiochhyjojnjmekekekekekekekekekekekekekekekekjjhtiu.rjl.eQtQtQtQtQtQtQtQtQtQtQtQtQtQtQtQtQtQtQtQtQtQtQtQt",
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
"QtQtQtQtQtQtQtQtQtQtQtQtQtQtQtQtQtQtQtQtQtQtQtQt.kjwjxjv.Zjpb4b4b4b4b4b4b4b4b4b4b4b4b4b4b4b4b4bZbZb4c7jv#KbUbJ#u#1b0cab7aZbGbtbtbtbtbtbtbtbtbtbtbtbtbtbtbtbtbtbtbtbtbtbtbtbtbtbtbtbtbtbtbtbtbtbtbtbtbtbtbtbtbtbtbtbtbtbtbtbtbtbtbtbtbtbtbtbtbtbtbtbtbtbtbtbtbtbtbtbtbtbtbtbtbtbtbtbtbtbtbtbtbtbtbtbtbtbtbtbtbtbtbtbtbtbtbtbtbtbtbtbtbtbtbtbtbtbtbtbtbtbtbtbtbtbtbtbtbtbtbtbtbtbtbtbtbtbtbtbtbtbtbtbtbGaZb7cab0#1#ubJbU#Kjvc7b4bZbZb4b4b4b4b4b4b4b4b4b4b4b4b4b4b4b4b4jp.Zjvjxjw.kQtQtQtQtQtQtQtQtQtQtQtQtQtQtQtQtQtQtQtQtQtQtQtQt",
"QtQtQtQtQtQtQtQtQtQtQtQtQtQtQtQtQtQtQtQtQtQtQtQtdrdKc9.Z.Z.Z.Z.YbUdMdMdMdMdMdMdMdMdMdMdMdMdMdMdMdMdMbU.Y.Zdudvbn#1b0cab7aZbGbtbtbtbtbtbtbtbtbtbtbtbtbtbtbtbtbtbtbtbtbtbtbtbtbtbtbtbtbtbtbtbtbtbtbtbtbtbtbtbtbtbtbtbtbtbtbtbtbtbtbtbtbtbtbtbtbtbtbtbtbtbtbtbtbtbtbtbtbtbtbtbtbtbtbtbtbtbtbtbtbtbtbtbtbtbtbtbtbtbtbtbtbtbtbtbtbtbtbtbtbtbtbtbtbtbtbtbtbtbtbtbtbtbtbtbtbtbtbtbtbtbtbtbtbtbtbtbtbtbtbtbtbGaZb7cab0#1bndvdu.Z.YbUdMdMdMdMdMdMdMdMdMdMdMdMdMdMdMdMdMbU.Y.Z.Z.Z.Zc9dKdrQtQtQtQtQtQtQtQtQtQtQtQtQtQtQtQtQtQtQtQtQtQtQtQt",
"QtQtQtQtQtQtQtQtQtQtQtQtQtQtQtQtQtQtQtQtQtQtQtQtdrdsjy.Z.ZdL.ZdMiPdPd7d7gwdPdPdPdPdPdPdPdPdPgwd7d7gwf#e.#LdudQbn#1b0cab7aZbGbtbtbtbtbtbtbtbtbtbtbtbtbtbtbtbtbtbtbtbtbtbtbtbtbtbtbtbtbtbtbtbtbtbtbtbtbtbtbtbtbtbtbtbtbtbtbtbtbtbtbtbtbtbtbtbtbtbtbtbtbtbtbtbtbtbtbtbtbtbtbtbtbtbtbtbtbtbtbtbtbtbtbtbtbtbtbtbtbtbtbtbtbtbtbtbtbtbtbtbtbtbtbtbtbtbtbtbtbtbtbtbtbtbtbtbtbtbtbtbtbtbtbtbtbtbtbtbtbtbtbtbtbGaZb7cab0#1bndQdu#Le.f#gwd7d7gwdPdPdPdPdPdPdPdPdPgwd7d7dPiPdM.ZdL.Z.ZjydsdrQtQtQtQtQtQtQtQtQtQtQtQtQtQtQtQtQtQtQtQtQtQtQtQt",
"QtQtQtQtQtQtQtQtQtQtQtQtQtQtQtQtQtQtQtQtQtQtQtQtd3itjz.Z.ZdL.ZdMdNdOdPdPdOdOdOdOdOdOdOdOdOdOdOdPdPdOdNdM#L#M#ubn#1b0cab7aZbGbtbtbtbtbtbtbtbtbtbtbtbtbtbtbtbtbtbtbtbtbtbtbtbtbtbtbtbtbtbtbtbtbtbtbtbtbtbtbtbtbtbtbtbtbtbtbtbtbtbtbtbtbtbtbtbtbtbtbtbtbtbtbtbtbtbtbtbtbtbtbtbtbtbtbtbtbtbtbtbtbtbtbtbtbtbtbtbtbtbtbtbtbtbtbtbtbtbtbtbtbtbtbtbtbtbtbtbtbtbtbtbtbtbtbtbtbtbtbtbtbtbtbtbtbtbtbtbtbtbtbtbtbGaZb7cab0#1bn#u#M#LdMdNdOdPdPdOdOdOdOdOdOdOdOdOdOdOdPdPdOdNdM.ZdL.Z.Zjzitd3QtQtQtQtQtQtQtQtQtQtQtQtQtQtQtQtQtQtQtQtQtQtQtQt",
"QtQtQtQtQtQtQtQtQtQtQtQtQtQtQtQtQtQtQtQtQtQtQtQtctekel.Z.Y.Y.ZjAjBjCeBg5jDjDjDjDjDjDjDjDjDjDjDg5eBjDjEeneAdM#v#u#1b0cab7aZbGbtbtbtbtbtbtbtbtbtbtbtbtbtbtbtbtbtbtbtbtbtbtbtbtbtbtbtbtbtbtbtbtbtbtbtbtbtbtbtbtbtbtbtbtbtbtbtbtbtbtbtbtbtbtbtbtbtbtbtbtbtbtbtbtbtbtbtbtbtbtbtbtbtbtbtbtbtbtbtbtbtbtbtbtbtbtbtbtbtbtbtbtbtbtbtbtbtbtbtbtbtbtbtbtbtbtbtbtbtbtbtbtbtbtbtbtbtbtbtbtbtbtbtbtbtbtbtbtbtbtbtbtbGaZb7cab0#1#u#vdMeAenjEjDeBg5jDjDjDjDjDjDjDjDjDjDjDg5eBjCjBjA.Z.Y.Y.ZelekctQtQtQtQtQtQtQtQtQtQtQtQtQtQtQtQtQtQtQtQtQtQtQtQt",
"QtQtQtQtQtQtQtQtQtQtQtQtQtQtQtQtQtQtQtQtQtQtQtQtctekel.ZdMjceAeKjFjGjHjIjJjJjJjJjJjJjJjJjJjJjJjejHiNjKh.jLjMeM#u#1b0cab7aZbGbtbtbtbtbtbtbtbtbtbtbtbtbtbtbtbtbtbtbtbtbtbtbtbtbtbtbtbtbtbtbtbtbtbtbtbtbtbtbtbtbtbtbtbtbtbtbtbtbtbtbtbtbtbtbtbtbtbtbtbtbtbtbtbtbtbtbtbtbtbtbtbtbtbtbtbtbtbtbtbtbtbtbtbtbtbtbtbtbtbtbtbtbtbtbtbtbtbtbtbtbtbtbtbtbtbtbtbtbtbtbtbtbtbtbtbtbtbtbtbtbtbtbtbtbtbtbtbtbtbtbtbtbGaZb7cab0#1#ueMjMjLh.jKiNjHjejJjJjJjJjJjJjJjJjJjJjJjIjHjGjFeKeAjcdM.ZelekctQtQtQtQtQtQtQtQtQtQtQtQtQtQtQtQtQtQtQtQtQtQtQtQt",
"QtQtQtQtQtQtQtQtQtQtQtQtQtQtQtQtQtQtQtQtQtQtQtQtctekel.ZdNdPazjNjOeWgEjPjQjRjRjRjRjRjRjRjRjRjRjSgEjTjUfajVd7gLe6#1b0cab7aZbGbtbtbtbtbtbtbtbtbtbtbtbtbtbtbtbtbtbtbtbtbtbtbtbtbtbtbtbtbtbtbtbtbtbtbtbtbtbtbtbtbtbtbtbtbtbtbtbtbtbtbtbtbtbtbtbtbtbtbtbtbtbtbtbtbtbtbtbtbtbtbtbtbtbtbtbtbtbtbtbtbtbtbtbtbtbtbtbtbtbtbtbtbtbtbtbtbtbtbtbtbtbtbtbtbtbtbtbtbtbtbtbtbtbtbtbtbtbtbtbtbtbtbtbtbtbtbtbtbtbtbtbtbGaZb7cab0#1e6gLd7jVfajUjTgEjSjRjRjRjRjRjRjRjRjRjRjQjPgEeWjOjNazdPdN.ZelekctQtQtQtQtQtQtQtQtQtQtQtQtQtQtQtQtQtQtQtQtQtQtQtQt",
"QtQtQtQtQtQtQtQtQtQtQtQtQtQtQtQtQtQtQtQtQtQtQtQtctekel#Lf#fLemfMiXfffOfifQfQfQfQfQfQfQfQfQfQfQfzfBfhe0eIeofkfD#v#1b0cab7aZbGbtbtbtbtbtbtbtbtbtbtbtbtbtbtbtbtbtbtbtbtbtbtbtbtbtbtbtbtbtbtbtbtbtbtbtbtbtbtbtbtbtbtbtbtbtbtbtbtbtbtbtbtbtbtbtbtbtbtbtbtbtbtbtbtbtbtbtbtbtbtbtbtbtbtbtbtbtbtbtbtbtbtbtbtbtbtbtbtbtbtbtbtbtbtbtbtbtbtbtbtbtbtbtbtbtbtbtbtbtbtbtbtbtbtbtbtbtbtbtbtbtbtbtbtbtbtbtbtbtbtbtbtbGaZb7cab0#1#vfDfkeoeIe0fhfBfzfQfQfQfQfQfQfQfQfQfQfQfifOffiXfMemfLf##LelekctQtQtQtQtQtQtQtQtQtQtQtQtQtQtQtQtQtQtQtQtQtQtQtQt",
"QtQtQtQtQtQtQtQtQtQtQtQtQtQtQtQtQtQtQtQtQtQtQtQtctekel#Lf#fuemfvfwfhfxfyfzggggggggggggggggggfAfOfxfdeWi1epfCfD#v#1b0cab7aZbGbtbtbtbtbtbtbtbtbtbtbtbtbtbtbtbtbtbtbtbtbtbtbtbtbtbtbtbtbtbtbtbtbtbtbtbtbtbtbtbtbtbtbtbtbtbtbtbtbtbtbtbtbtbtbtbtbtbtbtbtbtbtbtbtbtbtbtbtbtbtbtbtbtbtbtbtbtbtbtbtbtbtbtbtbtbtbtbtbtbtbtbtbtbtbtbtbtbtbtbtbtbtbtbtbtbtbtbtbtbtbtbtbtbtbtbtbtbtbtbtbtbtbtbtbtbtbtbtbtbtbtbtbGaZb7cab0#1#vfDfCepi1eWfdfxfOfAggggggggggggggggggfzfyfxfhfwfvemfuf##LelekctQtQtQtQtQtQtQtQtQtQtQtQtQtQtQtQtQtQtQtQtQtQtQtQt",
"QtQtQtQtQtQtQtQtQtQtQtQtQtQtQtQtQtQtQtQtQtQtQtQtctekel#Lf#fLemfajWiWghfzgbfjfjfjfjfjfjfjfjfjfjfeghf3jXjYeofkfl#v#1b0cab7aZbGbtbtbtbtbtbtbtbtbtbtbtbtbtbtbtbtbtbtbtbtbtbtbtbtbtbtbtbtbtbtbtbtbtbtbtbtbtbtbtbtbtbtbtbtbtbtbtbtbtbtbtbtbtbtbtbtbtbtbtbtbtbtbtbtbtbtbtbtbtbtbtbtbtbtbtbtbtbtbtbtbtbtbtbtbtbtbtbtbtbtbtbtbtbtbtbtbtbtbtbtbtbtbtbtbtbtbtbtbtbtbtbtbtbtbtbtbtbtbtbtbtbtbtbtbtbtbtbtbtbtbtbtbGaZb7cab0#1#vflfkeojYjXf3ghfefjfjfjfjfjfjfjfjfjfjgbfzghiWjWfaemfLf##LelekctQtQtQtQtQtQtQtQtQtQtQtQtQtQtQtQtQtQtQtQtQtQtQtQt",
"QtQtQtQtQtQtQtQtQtQtQtQtQtQtQtQtQtQtQtQtQtQtQtQtctekel#Lf#d8emfVfWfXfAf3dxfcfcfcfcfcfcfcfcfcfcfQfAfgeZeHeofkfl#v#1b0cab7aZbGbtbtbtbtbtbtbtbtbtbtbtbtbtbtbtbtbtbtbtbtbtbtbtbtbtbtbtbtbtbtbtbtbtbtbtbtbtbtbtbtbtbtbtbtbtbtbtbtbtbtbtbtbtbtbtbtbtbtbtbtbtbtbtbtbtbtbtbtbtbtbtbtbtbtbtbtbtbtbtbtbtbtbtbtbtbtbtbtbtbtbtbtbtbtbtbtbtbtbtbtbtbtbtbtbtbtbtbtbtbtbtbtbtbtbtbtbtbtbtbtbtbtbtbtbtbtbtbtbtbtbtbtbGaZb7cab0#1#vflfkeoeHeZfgfAfQfcfcfcfcfcfcfcfcfcfcdxf3fAfXfWfVemd8f##LelekctQtQtQtQtQtQtQtQtQtQtQtQtQtQtQtQtQtQtQtQtQtQtQtQt",
"QtQtQtQtQtQtQtQtQtQtQtQtQtQtQtQtQtQtQtQtQtQtQtQtctekel#Lf#d8emfVfWfXfAf3dxfcfcfcfcfcfcfcfcfcfcfQfAfgeZeHeofkfl#v#1b0cab7aZbGbtbtbtbtbtbtbtbtbtbtbtbtbtbtbtbtbtbtbtbtbtbtbtbtbtbtbtbtbtbtbtbtbtbtbtbtbtbtbtbtbtbtbtbtbtbtbtbtbtbtbtbtbtbtbtbtbtbtbtbtbtbtbtbtbtbtbtbtbtbtbtbtbtbtbtbtbtbtbtbtbtbtbtbtbtbtbtbtbtbtbtbtbtbtbtbtbtbtbtbtbtbtbtbtbtbtbtbtbtbtbtbtbtbtbtbtbtbtbtbtbtbtbtbtbtbtbtbtbtbtbtbtbGaZb7cab0#1#vflfkeoeHeZfgfAfQfcfcfcfcfcfcfcfcfcfcdxf3fAfXfWfVemd8f##LelekctQtQtQtQtQtQtQtQtQtQtQtQtQtQtQtQtQtQtQtQtQtQtQtQt",
"QtQtQtQtQtQtQtQtQtQtQtQtQtQtQtQtQtQtQtQtQtQtQtQtctekel#Lf#d8emfVfWfXfAf3dxfcfcfcfcfcfcfcfcfcfcfQfAfgeZeHeofkfl#v#1b0cab7aZbGbtbtbtbtbtbtbtbtbtbtbtbtbtbtbtbtbtbtbtbtbtbtbtbtbtbtbtbtbtbtbtbtbtbtbtbtbtbtbtbtbtbtbtbtbtbtbtbtbtbtbtbtbtbtbtbtbtbtbtbtbtbtbtbtbtbtbtbtbtbtbtbtbtbtbtbtbtbtbtbtbtbtbtbtbtbtbtbtbtbtbtbtbtbtbtbtbtbtbtbtbtbtbtbtbtbtbtbtbtbtbtbtbtbtbtbtbtbtbtbtbtbtbtbtbtbtbtbtbtbtbtbtbGaZb7cab0#1#vflfkeoeHeZfgfAfQfcfcfcfcfcfcfcfcfcfcdxf3fAfXfWfVemd8f##LelekctQtQtQtQtQtQtQtQtQtQtQtQtQtQtQtQtQtQtQtQtQtQtQtQt",
"QtQtQtQtQtQtQtQtQtQtQtQtQtQtQtQtQtQtQtQtQtQtQtQtctekel#Lf#d8emfVfWfXfAf3dxfcfcfcfcfcfcfcfcfcfcfQfAfgeZeHeofkfl#v#1b0cab7aZbGbtbtbtbtbtbtbtbtbtbtbtbtbtbtbtbtbtbtbtbtbtbtbtbtbtbtbtbtbtbtbtbtbtbtbtbtbtbtbtbtbtbtbtbtbtbtbtbtbtbtbtbtbtbtbtbtbtbtbtbtbtbtbtbtbtbtbtbtbtbtbtbtbtbtbtbtbtbtbtbtbtbtbtbtbtbtbtbtbtbtbtbtbtbtbtbtbtbtbtbtbtbtbtbtbtbtbtbtbtbtbtbtbtbtbtbtbtbtbtbtbtbtbtbtbtbtbtbtbtbtbtbtbGaZb7cab0#1#vflfkeoeHeZfgfAfQfcfcfcfcfcfcfcfcfcfcdxf3fAfXfWfVemd8f##LelekctQtQtQtQtQtQtQtQtQtQtQtQtQtQtQtQtQtQtQtQtQtQtQtQt",
"QtQtQtQtQtQtQtQtQtQtQtQtQtQtQtQtQtQtQtQtQtQtQtQtctekel#Lf#fLemfajWiWghfzgbfjfjfjfjfjfjfjfjfjfjfeghf3jXjYeofkfl#v#1b0cab7aZbGbtbtbtbtbtbtbtbtbtbtbtbtbtbtbtbtbtbtbtbtbtbtbtbtbtbtbtbtbtbtbtbtbtbtbtbtbtbtbtbtbtbtbtbtbtbtbtbtbtbtbtbtbtbtbtbtbtbtbtbtbtbtbtbtbtbtbtbtbtbtbtbtbtbtbtbtbtbtbtbtbtbtbtbtbtbtbtbtbtbtbtbtbtbtbtbtbtbtbtbtbtbtbtbtbtbtbtbtbtbtbtbtbtbtbtbtbtbtbtbtbtbtbtbtbtbtbtbtbtbtbtbtbGaZb7cab0#1#vflfkeojYjXf3ghfefjfjfjfjfjfjfjfjfjfjgbfzghiWjWfaemfLf##LelekctQtQtQtQtQtQtQtQtQtQtQtQtQtQtQtQtQtQtQtQtQtQtQtQt",
"QtQtQtQtQtQtQtQtQtQtQtQtQtQtQtQtQtQtQtQtQtQtQtQtctekel#Lf#fuemfvfwfhfxfyfzggggggggggggggggggfAfOfxfdeWi1epfCfD#v#1b0cab7aZbGbtbtbtbtbtbtbtbtbtbtbtbtbtbtbtbtbtbtbtbtbtbtbtbtbtbtbtbtbtbtbtbtbtbtbtbtbtbtbtbtbtbtbtbtbtbtbtbtbtbtbtbtbtbtbtbtbtbtbtbtbtbtbtbtbtbtbtbtbtbtbtbtbtbtbtbtbtbtbtbtbtbtbtbtbtbtbtbtbtbtbtbtbtbtbtbtbtbtbtbtbtbtbtbtbtbtbtbtbtbtbtbtbtbtbtbtbtbtbtbtbtbtbtbtbtbtbtbtbtbtbtbtbGaZb7cab0#1#vfDfCepi1eWfdfxfOfAggggggggggggggggggfzfyfxfhfwfvemfuf##LelekctQtQtQtQtQtQtQtQtQtQtQtQtQtQtQtQtQtQtQtQtQtQtQtQt",
"QtQtQtQtQtQtQtQtQtQtQtQtQtQtQtQtQtQtQtQtQtQtQtQtctekel#Lf#fLemfMiXfffOfifQfQfQfQfQfQfQfQfQfQfQfzfBfhe0eIeofkfD#v#1b0cab7aZbGbtbtbtbtbtbtbtbtbtbtbtbtbtbtbtbtbtbtbtbtbtbtbtbtbtbtbtbtbtbtbtbtbtbtbtbtbtbtbtbtbtbtbtbtbtbtbtbtbtbtbtbtbtbtbtbtbtbtbtbtbtbtbtbtbtbtbtbtbtbtbtbtbtbtbtbtbtbtbtbtbtbtbtbtbtbtbtbtbtbtbtbtbtbtbtbtbtbtbtbtbtbtbtbtbtbtbtbtbtbtbtbtbtbtbtbtbtbtbtbtbtbtbtbtbtbtbtbtbtbtbtbtbGaZb7cab0#1#vfDfkeoeIe0fhfBfzfQfQfQfQfQfQfQfQfQfQfQfifOffiXfMemfLf##LelekctQtQtQtQtQtQtQtQtQtQtQtQtQtQtQtQtQtQtQtQtQtQtQtQt",
"QtQtQtQtQtQtQtQtQtQtQtQtQtQtQtQtQtQtQtQtQtQtQtQtctekel.ZdNdPazjNjOeWgEjPjQjRjRjRjRjRjRjRjRjRjRjSgEjTjUfajVd7gLe6#1b0cab7aZbGbtbtbtbtbtbtbtbtbtbtbtbtbtbtbtbtbtbtbtbtbtbtbtbtbtbtbtbtbtbtbtbtbtbtbtbtbtbtbtbtbtbtbtbtbtbtbtbtbtbtbtbtbtbtbtbtbtbtbtbtbtbtbtbtbtbtbtbtbtbtbtbtbtbtbtbtbtbtbtbtbtbtbtbtbtbtbtbtbtbtbtbtbtbtbtbtbtbtbtbtbtbtbtbtbtbtbtbtbtbtbtbtbtbtbtbtbtbtbtbtbtbtbtbtbtbtbtbtbtbtbtbtbGaZb7cab0#1e6gLd7jVfajUjTgEjSjRjRjRjRjRjRjRjRjRjRjQjPgEeWjOjNazdPdN.ZelekctQtQtQtQtQtQtQtQtQtQtQtQtQtQtQtQtQtQtQtQtQtQtQtQt",
"QtQtQtQtQtQtQtQtQtQtQtQtQtQtQtQtQtQtQtQtQtQtQtQtctekel.ZdMjceAeKjFjGjHjIjJjJjJjJjJjJjJjJjJjJjJjejHiNjKh.jLjMeM#u#1b0cab7aZbGbtbtbtbtbtbtbtbtbtbtbtbtbtbtbtbtbtbtbtbtbtbtbtbtbtbtbtbtbtbtbtbtbtbtbtbtbtbtbtbtbtbtbtbtbtbtbtbtbtbtbtbtbtbtbtbtbtbtbtbtbtbtbtbtbtbtbtbtbtbtbtbtbtbtbtbtbtbtbtbtbtbtbtbtbtbtbtbtbtbtbtbtbtbtbtbtbtbtbtbtbtbtbtbtbtbtbtbtbtbtbtbtbtbtbtbtbtbtbtbtbtbtbtbtbtbtbtbtbtbtbtbtbGaZb7cab0#1#ueMjMjLh.jKiNjHjejJjJjJjJjJjJjJjJjJjJjJjIjHjGjFeKeAjcdM.ZelekctQtQtQtQtQtQtQtQtQtQtQtQtQtQtQtQtQtQtQtQtQtQtQtQt",
"QtQtQtQtQtQtQtQtQtQtQtQtQtQtQtQtQtQtQtQtQtQtQtQtctekel.Z.Y.Y.ZjAjBjCeBg5jDjDjDjDjDjDjDjDjDjDjDg5eBjDjEeneAdM#v#u#1b0cab7aZbGbtbtbtbtbtbtbtbtbtbtbtbtbtbtbtbtbtbtbtbtbtbtbtbtbtbtbtbtbtbtbtbtbtbtbtbtbtbtbtbtbtbtbtbtbtbtbtbtbtbtbtbtbtbtbtbtbtbtbtbtbtbtbtbtbtbtbtbtbtbtbtbtbtbtbtbtbtbtbtbtbtbtbtbtbtbtbtbtbtbtbtbtbtbtbtbtbtbtbtbtbtbtbtbtbtbtbtbtbtbtbtbtbtbtbtbtbtbtbtbtbtbtbtbtbtbtbtbtbtbtbtbtbGaZb7cab0#1#u#vdMeAenjEjDeBg5jDjDjDjDjDjDjDjDjDjDjDg5eBjCjBjA.Z.Y.Y.ZelekctQtQtQtQtQtQtQtQtQtQtQtQtQtQtQtQtQtQtQtQtQtQtQtQt",
"QtQtQtQtQtQtQtQtQtQtQtQtQtQtQtQtQtQtQtQtQtQtQtQtd3itjz.Z.ZdL.ZdMdNdOdPdPdOdOdOdOdOdOdOdOdOdOdOdPdPdOdNdM#L#M#ubn#1b0cab7aZbGbtbtbtbtbtbtbtbtbtbtbtbtbtbtbtbtbtbtbtbtbtbtbtbtbtbtbtbtbtbtbtbtbtbtbtbtbtbtbtbtbtbtbtbtbtbtbtbtbtbtbtbtbtbtbtbtbtbtbtbtbtbtbtbtbtbtbtbtbtbtbtbtbtbtbtbtbtbtbtbtbtbtbtbtbtbtbtbtbtbtbtbtbtbtbtbtbtbtbtbtbtbtbtbtbtbtbtbtbtbtbtbtbtbtbtbtbtbtbtbtbtbtbtbtbtbtbtbtbtbtbtbtbGaZb7cab0#1bn#u#M#LdMdNdOdPdPdOdOdOdOdOdOdOdOdOdOdOdPdPdOdNdM.ZdL.Z.Zjzitd3QtQtQtQtQtQtQtQtQtQtQtQtQtQtQtQtQtQtQtQtQtQtQtQt",
"QtQtQtQtQtQtQtQtQtQtQtQtQtQtQtQtQtQtQtQtQtQtQtQtdrdsjy.Z.ZdL.ZdMiPdPd7d7gwdPdPdPdPdPdPdPdPdPgwd7d7gwf#e.#LdudQbn#1b0cab7aZbGbtbtbtbtbtbtbtbtbtbtbtbtbtbtbtbtbtbtbtbtbtbtbtbtbtbtbtbtbtbtbtbtbtbtbtbtbtbtbtbtbtbtbtbtbtbtbtbtbtbtbtbtbtbtbtbtbtbtbtbtbtbtbtbtbtbtbtbtbtbtbtbtbtbtbtbtbtbtbtbtbtbtbtbtbtbtbtbtbtbtbtbtbtbtbtbtbtbtbtbtbtbtbtbtbtbtbtbtbtbtbtbtbtbtbtbtbtbtbtbtbtbtbtbtbtbtbtbtbtbtbtbtbGaZb7cab0#1bndQdu#Le.f#gwd7d7gwdPdPdPdPdPdPdPdPdPgwd7d7dPiPdM.ZdL.Z.ZjydsdrQtQtQtQtQtQtQtQtQtQtQtQtQtQtQtQtQtQtQtQtQtQtQtQt",
"QtQtQtQtQtQtQtQtQtQtQtQtQtQtQtQtQtQtQtQtQtQtQtQtdrdKc9.Z.Z.Z.Z.YbUdMdMdMdMdMdMdMdMdMdMdMdMdMdMdMdMdMbU.Y.Zdudvbn#1b0cab7aZbGbtbtbtbtbtbtbtbtbtbtbtbtbtbtbtbtbtbtbtbtbtbtbtbtbtbtbtbtbtbtbtbtbtbtbtbtbtbtbtbtbtbtbtbtbtbtbtbtbtbtbtbtbtbtbtbtbtbtbtbtbtbtbtbtbtbtbtbtbtbtbtbtbtbtbtbtbtbtbtbtbtbtbtbtbtbtbtbtbtbtbtbtbtbtbtbtbtbtbtbtbtbtbtbtbtbtbtbtbtbtbtbtbtbtbtbtbtbtbtbtbtbtbtbtbtbtbtbtbtbtbtbtbGaZb7cab0#1bndvdu.Z.YbUdMdMdMdMdMdMdMdMdMdMdMdMdMdMdMdMdMbU.Y.Z.Z.Z.Zc9dKdrQtQtQtQtQtQtQtQtQtQtQtQtQtQtQtQtQtQtQtQtQtQtQtQt",
"QtQtQtQtQtQtQtQtQtQtQtQtQtQtQtQtQtQtQtQtQtQtQtQt.kjwjxjv.Zjpb4b4b4b4b4b4b4b4b4b4b4b4b4b4b4b4b4bZbZb4c7jv#KbUbJ#u#1b0cab7aZbGbtbtbtbtbtbtbtbtbtbtbtbtbtbtbtbtbtbtbtbtbtbtbtbtbtbtbtbtbtbtbtbtbtbtbtbtbtbtbtbtbtbtbtbtbtbtbtbtbtbtbtbtbtbtbtbtbtbtbtbtbtbtbtbtbtbtbtbtbtbtbtbtbtbtbtbtbtbtbtbtbtbtbtbtbtbtbtbtbtbtbtbtbtbtbtbtbtbtbtbtbtbtbtbtbtbtbtbtbtbtbtbtbtbtbtbtbtbtbtbtbtbtbtbtbtbtbtbtbtbtbtbtbGaZb7cab0#1#ubJbU#Kjvc7b4bZbZb4b4b4b4b4b4b4b4b4b4b4b4b4b4b4b4b4jp.Zjvjxjw.kQtQtQtQtQtQtQtQtQtQtQtQtQtQtQtQtQtQtQtQtQtQtQtQt",
"QtQtQtQtQtQtQtQtQtQtQtQtQtQtQtQtQtQtQtQtQtQtQtQt.6hVbjiejrjubYbYbYbYbYbYbYbYbYbYbYbYbYbYbYbYbYbBch.JaPjkjv#M#ubn#1b0cab7aZbGbtbtbtbtbtbtbtbtbtbtbtbtbtbtbtbtbtbtbtbtbtbtbtbtbtbtbtbtbtbtbtbtbtbtbtbtbtbtbtbtbtbtbtbtbtbtbtbtbtbtbtbtbtbtbtbtbtbtbtbtbtbtbtbtbtbtbtbtbtbtbtbtbtbtbtbtbtbtbtbtbtbtbtbtbtbtbtbtbtbtbtbtbtbtbtbtbtbtbtbtbtbtbtbtbtbtbtbtbtbtbtbtbtbtbtbtbtbtbtbtbtbtbtbtbtbtbtbtbtbtbtbtbGaZb7cab0#1bn#u#MjvjkaP.JchbBbYbYbYbYbYbYbYbYbYbYbYbYbYbYbYbYbYjujriebjhV.6QtQtQtQtQtQtQtQtQtQtQtQtQtQtQtQtQtQtQtQtQtQtQtQt",
"QtQtQtQtQtQtQtQtQtQtQtQtQtQtQtQtQtQtQtQtQtQtQtQtibct.lcJhR#Qaaaaaaaaaaaaaaaaaaaaaaaaaaaaaaaaaacoh9bNjoaPc7#M#ubn#1b0cab7aZbGbtbtbtbtbtbtbtbtbtbtbtbtbtbtbtbtbtbtbtbtbtbtbtbtbtbtbtbtbtbtbtbtbtbtbtbtbtbtbtbtbtbtbtbtbtbtbtbtbtbtbtbtbtbtbtbtbtbtbtbtbtbtbtbtbtbtbtbtbtbtbtbtbtbtbtbtbtbtbtbtbtbtbtbtbtbtbtbtbtbtbtbtbtbtbtbtbtbtbtbtbtbtbtbtbtbtbtbtbtbtbtbtbtbtbtbtbtbtbtbtbtbtbtbtbtbtbtbtbtbtbtbtbGaZb7cab0#1bn#u#Mc7aPjobNh9coaaaaaaaaaaaaaaaaaaaaaaaaaaaaaaaaaa#QhRcJ.lctibQtQtQtQtQtQtQtQtQtQtQtQtQtQtQtQtQtQtQtQtQtQtQtQt",
"QtQtQtQtQtQtQtQtQtQtQtQtQtQtQtQtQtQtQtQtQtQtQtQtQtQtQtQtQtQtQtQtQtQtQtQtQtQtQtQtQtQtQtQtQtQtQtQtQtQtbN.Jb4#M#ubn#1b0cab7aZbGbtbtbtbtbtbtbtbtbtbtbtbtbtbtbtbtbtbtbtbtbtbtbtbtbtbtbtbtbtbtbtbtbtbtbtbtbtbtbtbtbtbtbtbtbtbtbtbtbtbtbtbtbtbtbtbtbtbtbtbtbtbtbtbtbtbtbtbtbtbtbtbtbtbtbtbtbtbtbtbtbtbtbtbtbtbtbtbtbtbtbtbtbtbtbtbtbtbtbtbtbtbtbtbtbtbtbtbtbtbtbtbtbtbtbtbtbtbtbtbtbtbtbtbtbtbtbtbtbtbtbtbtbGaZb7cab0#1bn#u#Mb4.JbNQtQtQtQtQtQtQtQtQtQtQtQtQtQtQtQtQtQtQtQtQtQtQtQtQtQtQtQtQtQtQtQtQtQtQtQtQtQtQtQtQtQtQtQtQtQtQtQtQtQt",
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
"QtQtQtQtQtQtQtQtQtQtQtQtQtQtQtQtQtQtQtQtQtQt.j.jQtQtQtQtQtQtQtQtQtQtQtQtQtQtQtQtQtQtQtQtQtQtQtQtQtQt.li.bZ#M#ubn#1b0cab7aZbGbtbtbtbtbtbtbtbtbtbtbtbtbtbtbtbtbtbtbtbtbtbtbtbtbtbtbtbtbtbtbtbtbtbtbtbtbtbtbtbtbtbtbtbtbtbtbtbtbtbtbtbtbtbtbtbtbtbtbtbtbtbtbtbtbtbtbtbtbtbtbtbtbtbtbtbtbtbtbtbtbtbtbtbtbtbtbtbtbtbtbtbtbtbtbtbtbtbtbtbtbtbtbtbtbtbtbtbtbtbtbtbtbtbtbtbtbtbtbtbtbtbtbtbtbtbtbtbtbtbtbtbtbGaZb7cab0#1bn#u#MbZi..lQtQtQtQtQtQtQtQtQtQtQtQtQtQtQtQtQtQtQtQtQtQtQtQtQtQt.j.jQtQtQtQtQtQtQtQtQtQtQtQtQtQtQtQtQtQtQtQtQtQt",
"QtQtQtQtQtQtQtQtQtQtQtQtQtQtQtQtQtQtQtQtQtQtQtQt.i.ea#d3drd3ctctctctctctctctctctctctctctctctctjq.d#ThSjrcx#M#ubn#1b0cab7aZbGbtbtbtbtbtbtbtbtbtbtbtbtbtbtbtbtbtbtbtbtbtbtbtbtbtbtbtbtbtbtbtbtbtbtbtbtbtbtbtbtbtbtbtbtbtbtbtbtbtbtbtbtbtbtbtbtbtbtbtbtbtbtbtbtbtbtbtbtbtbtbtbtbtbtbtbtbtbtbtbtbtbtbtbtbtbtbtbtbtbtbtbtbtbtbtbtbtbtbtbtbtbtbtbtbtbtbtbtbtbtbtbtbtbtbtbtbtbtbtbtbtbtbtbtbtbtbtbtbtbtbtbtbGaZb7cab0#1bn#u#McxjrhS#T.djqctctctctctctctctctctctctctctctctctd3drd3a#.e.iQtQtQtQtQtQtQtQtQtQtQtQtQtQtQtQtQtQtQtQtQtQtQtQt",
"QtQtQtQtQtQtQtQtQtQtQtQtQtQtQtQtQtQtQtQtQtQtQtQt.ejl.riuhtjjekekekekekekekekekekekekekekekekjmjnjohychiojp#M#ubn#1b0cab7aZbGbtbtbtbtbtbtbtbtbtbtbtbtbtbtbtbtbtbtbtbtbtbtbtbtbtbtbtbtbtbtbtbtbtbtbtbtbtbtbtbtbtbtbtbtbtbtbtbtbtbtbtbtbtbtbtbtbtbtbtbtbtbtbtbtbtbtbtbtbtbtbtbtbtbtbtbtbtbtbtbtbtbtbtbtbtbtbtbtbtbtbtbtbtbtbtbtbtbtbtbtbtbtbtbtbtbtbtbtbtbtbtbtbtbtbtbtbtbtbtbtbtbtbtbtbtbtbtbtbtbtbtbtbGaZb7cab0#1bn#u#Mjpiochhyjojnjmekekekekekekekekekekekekekekekekjjhtiu.rjl.eQtQtQtQtQtQtQtQtQtQtQtQtQtQtQtQtQtQtQtQtQtQtQtQt",
"QtQtQtQtQtQtQtQtQtQtQtQtQtQtQtQtQtQtQtQtQtQtQtQta#.rhOivc8jkelelelelelelelelelelelelelelelelel#OhzelhpbOhC#MbJbn#1b0cab7aZbGbtbtbtbtbtbtbtbtbtbtbtbtbtbtbtbtbtbtbtbtbtbtbtbtbtbtbtbtbtbtbtbtbtbtbtbtbtbtbtbtbtbtbtbtbtbtbtbtbtbtbtbtbtbtbtbtbtbtbtbtbtbtbtbtbtbtbtbtbtbtbtbtbtbtbtbtbtbtbtbtbtbtbtbtbtbtbtbtbtbtbtbtbtbtbtbtbtbtbtbtbtbtbtbtbtbtbtbtbtbtbtbtbtbtbtbtbtbtbtbtbtbtbtbtbtbtbtbtbtbtbtbtbGaZb7cab0#1bnbJ#MhCbOhpelhz#Oeleleleleleleleleleleleleleleleleljkc8ivhO.ra#QtQtQtQtQtQtQtQtQtQtQtQtQtQtQtQtQtQtQtQtQtQtQtQt",
"QtQtQtQtQtQtQtQtQtQtQtQtQtQtQtQtQtQtQtQtQtQtQtQtd3iuiv.Z.Z.Z.Z.Z.Z#L#L#L#L#L#L#L#L#L#L#L#L#L#L#L#L#L.Z.Z.Zdudv#u#1b0cab7aZbGbtbtbtbtbtbtbtbtbtbtbtbtbtbtbtbtbtbtbtbtbtbtbtbtbtbtbtbtbtbtbtbtbtbtbtbtbtbtbtbtbtbtbtbtbtbtbtbtbtbtbtbtbtbtbtbtbtbtbtbtbtbtbtbtbtbtbtbtbtbtbtbtbtbtbtbtbtbtbtbtbtbtbtbtbtbtbtbtbtbtbtbtbtbtbtbtbtbtbtbtbtbtbtbtbtbtbtbtbtbtbtbtbtbtbtbtbtbtbtbtbtbtbtbtbtbtbtbtbtbtbtbtbGaZb7cab0#1#udvdu.Z.Z.Z#L#L#L#L#L#L#L#L#L#L#L#L#L#L#L#L#L.Z.Z.Z.Z.Z.Ziviud3QtQtQtQtQtQtQtQtQtQtQtQtQtQtQtQtQtQtQtQtQtQtQtQt",
"QtQtQtQtQtQtQtQtQtQtQtQtQtQtQtQtQtQtQtQtQtQtQtQtdrhtc8.Z.Z.Z.ZbUjcd6f#f#f#f#f#f#f#f#f#f#f#f#f#f#f#f#eLdM.ZdudQbn#1b0cab7aZbGbtbtbtbtbtbtbtbtbtbtbtbtbtbtbtbtbtbtbtbtbtbtbtbtbtbtbtbtbtbtbtbtbtbtbtbtbtbtbtbtbtbtbtbtbtbtbtbtbtbtbtbtbtbtbtbtbtbtbtbtbtbtbtbtbtbtbtbtbtbtbtbtbtbtbtbtbtbtbtbtbtbtbtbtbtbtbtbtbtbtbtbtbtbtbtbtbtbtbtbtbtbtbtbtbtbtbtbtbtbtbtbtbtbtbtbtbtbtbtbtbtbtbtbtbtbtbtbtbtbtbtbtbGaZb7cab0#1bndQdu.ZdMeLf#f#f#f#f#f#f#f#f#f#f#f#f#f#f#f#d6jcbU.Z.Z.Z.Zc8htdrQtQtQtQtQtQtQtQtQtQtQtQtQtQtQtQtQtQtQtQtQtQtQtQt",
"QtQtQtQtQtQtQtQtQtQtQtQtQtQtQtQtQtQtQtQtQtQtQtQtd3jjjk.Z.ZeA.ZdMf#d8fufLd8d8d8d8d8d8d8d8d8d8d8fLfud8dObo#L#M#ubn#1b0cab7aZbGbtbtbtbtbtbtbtbtbtbtbtbtbtbtbtbtbtbtbtbtbtbtbtbtbtbtbtbtbtbtbtbtbtbtbtbtbtbtbtbtbtbtbtbtbtbtbtbtbtbtbtbtbtbtbtbtbtbtbtbtbtbtbtbtbtbtbtbtbtbtbtbtbtbtbtbtbtbtbtbtbtbtbtbtbtbtbtbtbtbtbtbtbtbtbtbtbtbtbtbtbtbtbtbtbtbtbtbtbtbtbtbtbtbtbtbtbtbtbtbtbtbtbtbtbtbtbtbtbtbtbtbtbGaZb7cab0#1bn#u#M#LbodOd8fufLd8d8d8d8d8d8d8d8d8d8d8fLfud8f#dM.ZeA.Z.Zjkjjd3QtQtQtQtQtQtQtQtQtQtQtQtQtQtQtQtQtQtQtQtQtQtQtQt",
"QtQtQtQtQtQtQtQtQtQtQtQtQtQtQtQtQtQtQtQtQtQtQtQtctekel.Z.Z.Z.ZeAazemememememememememememememememememazeA.ZbU#v#u#1b0cab7aZbGbtbtbtbtbtbtbtbtbtbtbtbtbtbtbtbtbtbtbtbtbtbtbtbtbtbtbtbtbtbtbtbtbtbtbtbtbtbtbtbtbtbtbtbtbtbtbtbtbtbtbtbtbtbtbtbtbtbtbtbtbtbtbtbtbtbtbtbtbtbtbtbtbtbtbtbtbtbtbtbtbtbtbtbtbtbtbtbtbtbtbtbtbtbtbtbtbtbtbtbtbtbtbtbtbtbtbtbtbtbtbtbtbtbtbtbtbtbtbtbtbtbtbtbtbtbtbtbtbtbtbtbtbGaZb7cab0#1#u#vbU.ZeAazemememememememememememememememememazeA.Z.Z.Z.ZelekctQtQtQtQtQtQtQtQtQtQtQtQtQtQtQtQtQtQtQtQtQtQtQtQt",
"QtQtQtQtQtQtQtQtQtQtQtQtQtQtQtQtQtQtQtQtQtQtQtQtctekel.ZbUdMeAjhjdj#fvi9fVfVfVfVfVfVfVfVfVfVfVfMfvfaeTeBemjcji#u#1b0cab7aZbGbtbtbtbtbtbtbtbtbtbtbtbtbtbtbtbtbtbtbtbtbtbtbtbtbtbtbtbtbtbtbtbtbtbtbtbtbtbtbtbtbtbtbtbtbtbtbtbtbtbtbtbtbtbtbtbtbtbtbtbtbtbtbtbtbtbtbtbtbtbtbtbtbtbtbtbtbtbtbtbtbtbtbtbtbtbtbtbtbtbtbtbtbtbtbtbtbtbtbtbtbtbtbtbtbtbtbtbtbtbtbtbtbtbtbtbtbtbtbtbtbtbtbtbtbtbtbtbtbtbtbtbtbGaZb7cab0#1#ujijcemeBeTfafvfMfVfVfVfVfVfVfVfVfVfVfVi9fvj#jdjheAdMbU.ZelekctQtQtQtQtQtQtQtQtQtQtQtQtQtQtQtQtQtQtQtQtQtQtQtQt",
"QtQtQtQtQtQtQtQtQtQtQtQtQtQtQtQtQtQtQtQtQtQtQtQtctekel.Zjcf#azjdjegIfwj.i7fWfWfWfWfWfWfWfWfWfWfNfwfbeUeCenjfjge6#1b0cab7aZbGbtbtbtbtbtbtbtbtbtbtbtbtbtbtbtbtbtbtbtbtbtbtbtbtbtbtbtbtbtbtbtbtbtbtbtbtbtbtbtbtbtbtbtbtbtbtbtbtbtbtbtbtbtbtbtbtbtbtbtbtbtbtbtbtbtbtbtbtbtbtbtbtbtbtbtbtbtbtbtbtbtbtbtbtbtbtbtbtbtbtbtbtbtbtbtbtbtbtbtbtbtbtbtbtbtbtbtbtbtbtbtbtbtbtbtbtbtbtbtbtbtbtbtbtbtbtbtbtbtbtbtbtbGaZb7cab0#1e6jgjfeneCeUfbfwfNfWfWfWfWfWfWfWfWfWfWi7j.fwgIjejdazf#jc.ZelekctQtQtQtQtQtQtQtQtQtQtQtQtQtQtQtQtQtQtQtQtQtQtQtQt",
"QtQtQtQtQtQtQtQtQtQtQtQtQtQtQtQtQtQtQtQtQtQtQtQtctekel#Ld6d8emj#gIjafhgbiTfXfXfXfXfXfXfXfXfXfXfffhfceVeDeojbi0#v#1b0cab7aZbGbtbtbtbtbtbtbtbtbtbtbtbtbtbtbtbtbtbtbtbtbtbtbtbtbtbtbtbtbtbtbtbtbtbtbtbtbtbtbtbtbtbtbtbtbtbtbtbtbtbtbtbtbtbtbtbtbtbtbtbtbtbtbtbtbtbtbtbtbtbtbtbtbtbtbtbtbtbtbtbtbtbtbtbtbtbtbtbtbtbtbtbtbtbtbtbtbtbtbtbtbtbtbtbtbtbtbtbtbtbtbtbtbtbtbtbtbtbtbtbtbtbtbtbtbtbtbtbtbtbtbtbtbGaZb7cab0#1#vi0jbeoeDeVfcfhfffXfXfXfXfXfXfXfXfXfXiTgbfhjagIj#emd8d6#LelekctQtQtQtQtQtQtQtQtQtQtQtQtQtQtQtQtQtQtQtQtQtQtQtQt",
"QtQtQtQtQtQtQtQtQtQtQtQtQtQtQtQtQtQtQtQtQtQtQtQtctekel#Lf#fuemfvfwfhfxfyfzfAfAfAfAfAfAfAfAfAfAfOfxfdeWeEepfCfD#v#1b0cab7aZbGbtbtbtbtbtbtbtbtbtbtbtbtbtbtbtbtbtbtbtbtbtbtbtbtbtbtbtbtbtbtbtbtbtbtbtbtbtbtbtbtbtbtbtbtbtbtbtbtbtbtbtbtbtbtbtbtbtbtbtbtbtbtbtbtbtbtbtbtbtbtbtbtbtbtbtbtbtbtbtbtbtbtbtbtbtbtbtbtbtbtbtbtbtbtbtbtbtbtbtbtbtbtbtbtbtbtbtbtbtbtbtbtbtbtbtbtbtbtbtbtbtbtbtbtbtbtbtbtbtbtbtbtbGaZb7cab0#1#vfDfCepeEeWfdfxfOfAfAfAfAfAfAfAfAfAfAfzfyfxfhfwfvemfuf##LelekctQtQtQtQtQtQtQtQtQtQtQtQtQtQtQtQtQtQtQtQtQtQtQtQt",
"QtQtQtQtQtQtQtQtQtQtQtQtQtQtQtQtQtQtQtQtQtQtQtQtctekel#Lf#fLemi9j.gbfygofhf3f3f3f3f3f3f3f3f3fYfifyfeeXeFeofCfD#v#1b0cab7aZbGbtbtbtbtbtbtbtbtbtbtbtbtbtbtbtbtbtbtbtbtbtbtbtbtbtbtbtbtbtbtbtbtbtbtbtbtbtbtbtbtbtbtbtbtbtbtbtbtbtbtbtbtbtbtbtbtbtbtbtbtbtbtbtbtbtbtbtbtbtbtbtbtbtbtbtbtbtbtbtbtbtbtbtbtbtbtbtbtbtbtbtbtbtbtbtbtbtbtbtbtbtbtbtbtbtbtbtbtbtbtbtbtbtbtbtbtbtbtbtbtbtbtbtbtbtbtbtbtbtbtbtbtbGaZb7cab0#1#vfDfCeoeFeXfefyfifYf3f3f3f3f3f3f3f3f3fhgofygbj.i9emfLf##LelekctQtQtQtQtQtQtQtQtQtQtQtQtQtQtQtQtQtQtQtQtQtQtQtQt",
"QtQtQtQtQtQtQtQtQtQtQtQtQtQtQtQtQtQtQtQtQtQtQtQtctekel#Lf#d8emfVi7iTfzfhi8dxdxdxdxdxdxdxdxdxdxfPfzffeYeGeofkfl#v#1b0cab7aZbGbtbtbtbtbtbtbtbtbtbtbtbtbtbtbtbtbtbtbtbtbtbtbtbtbtbtbtbtbtbtbtbtbtbtbtbtbtbtbtbtbtbtbtbtbtbtbtbtbtbtbtbtbtbtbtbtbtbtbtbtbtbtbtbtbtbtbtbtbtbtbtbtbtbtbtbtbtbtbtbtbtbtbtbtbtbtbtbtbtbtbtbtbtbtbtbtbtbtbtbtbtbtbtbtbtbtbtbtbtbtbtbtbtbtbtbtbtbtbtbtbtbtbtbtbtbtbtbtbtbtbtbtbGaZb7cab0#1#vflfkeoeGeYfffzfPdxdxdxdxdxdxdxdxdxdxi8fhfziTi7fVemd8f##LelekctQtQtQtQtQtQtQtQtQtQtQtQtQtQtQtQtQtQtQtQtQtQtQtQt",
"QtQtQtQtQtQtQtQtQtQtQtQtQtQtQtQtQtQtQtQtQtQtQtQtctekel#Lf#d8emfVfWfXfAf3dxfcfcfcfcfcfcfcfcfcfcfQfAfgeZeHeofkfl#v#1b0cab7aZbGbtbtbtbtbtbtbtbtbtbtbtbtbtbtbtbtbtbtbtbtbtbtbtbtbtbtbtbtbtbtbtbtbtbtbtbtbtbtbtbtbtbtbtbtbtbtbtbtbtbtbtbtbtbtbtbtbtbtbtbtbtbtbtbtbtbtbtbtbtbtbtbtbtbtbtbtbtbtbtbtbtbtbtbtbtbtbtbtbtbtbtbtbtbtbtbtbtbtbtbtbtbtbtbtbtbtbtbtbtbtbtbtbtbtbtbtbtbtbtbtbtbtbtbtbtbtbtbtbtbtbtbtbGaZb7cab0#1#vflfkeoeHeZfgfAfQfcfcfcfcfcfcfcfcfcfcdxf3fAfXfWfVemd8f##LelekctQtQtQtQtQtQtQtQtQtQtQtQtQtQtQtQtQtQtQtQtQtQtQtQt",
"QtQtQtQtQtQtQtQtQtQtQtQtQtQtQtQtQtQtQtQtQtQtQtQtctekel#Lf#d8emfVfWfXfAf3dxfcfcfcfcfcfcfcfcfcfcfQfAfgeZeHeofkfl#v#1b0cab7aZbGbtbtbtbtbtbtbtbtbtbtbtbtbtbtbtbtbtbtbtbtbtbtbtbtbtbtbtbtbtbtbtbtbtbtbtbtbtbtbtbtbtbtbtbtbtbtbtbtbtbtbtbtbtbtbtbtbtbtbtbtbtbtbtbtbtbtbtbtbtbtbtbtbtbtbtbtbtbtbtbtbtbtbtbtbtbtbtbtbtbtbtbtbtbtbtbtbtbtbtbtbtbtbtbtbtbtbtbtbtbtbtbtbtbtbtbtbtbtbtbtbtbtbtbtbtbtbtbtbtbtbtbtbGaZb7cab0#1#vflfkeoeHeZfgfAfQfcfcfcfcfcfcfcfcfcfcdxf3fAfXfWfVemd8f##LelekctQtQtQtQtQtQtQtQtQtQtQtQtQtQtQtQtQtQtQtQtQtQtQtQt",
"QtQtQtQtQtQtQtQtQtQtQtQtQtQtQtQtQtQtQtQtQtQtQtQtctekel#Lf#d8emfVfWfXfAf3dxfcfcfcfcfcfcfcfcfcfcfQfAfgeZeHeofkfl#v#1b0cab7aZbGbtbtbtbtbtbtbtbtbtbtbtbtbtbtbtbtbtbtbtbtbtbtbtbtbtbtbtbtbtbtbtbtbtbtbtbtbtbtbtbtbtbtbtbtbtbtbtbtbtbtbtbtbtbtbtbtbtbtbtbtbtbtbtbtbtbtbtbtbtbtbtbtbtbtbtbtbtbtbtbtbtbtbtbtbtbtbtbtbtbtbtbtbtbtbtbtbtbtbtbtbtbtbtbtbtbtbtbtbtbtbtbtbtbtbtbtbtbtbtbtbtbtbtbtbtbtbtbtbtbtbtbtbGaZb7cab0#1#vflfkeoeHeZfgfAfQfcfcfcfcfcfcfcfcfcfcdxf3fAfXfWfVemd8f##LelekctQtQtQtQtQtQtQtQtQtQtQtQtQtQtQtQtQtQtQtQtQtQtQtQt",
"QtQtQtQtQtQtQtQtQtQtQtQtQtQtQtQtQtQtQtQtQtQtQtQtctekel#Lf#d8emfVi5dmfdgaiWiWiWiWiWiWiWiWiWiWiWfYfdfji6eGeofkfl#v#1b0cab7aZbGbtbtbtbtbtbtbtbtbtbtbtbtbtbtbtbtbtbtbtbtbtbtbtbtbtbtbtbtbtbtbtbtbtbtbtbtbtbtbtbtbtbtbtbtbtbtbtbtbtbtbtbtbtbtbtbtbtbtbtbtbtbtbtbtbtbtbtbtbtbtbtbtbtbtbtbtbtbtbtbtbtbtbtbtbtbtbtbtbtbtbtbtbtbtbtbtbtbtbtbtbtbtbtbtbtbtbtbtbtbtbtbtbtbtbtbtbtbtbtbtbtbtbtbtbtbtbtbtbtbtbtbtbGaZb7cab0#1#vflfkeoeGi6fjfdfYiWiWiWiWiWiWiWiWiWiWiWgafddmi5fVemd8f##LelekctQtQtQtQtQtQtQtQtQtQtQtQtQtQtQtQtQtQtQtQtQtQtQtQt",
"QtQtQtQtQtQtQtQtQtQtQtQtQtQtQtQtQtQtQtQtQtQtQtQtctekel#Lf#fLemfvgmfQi2i3fegagagagagagagagagagagoi2fAi4gqepfCfD#v#1b0cab7aZbGbtbtbtbtbtbtbtbtbtbtbtbtbtbtbtbtbtbtbtbtbtbtbtbtbtbtbtbtbtbtbtbtbtbtbtbtbtbtbtbtbtbtbtbtbtbtbtbtbtbtbtbtbtbtbtbtbtbtbtbtbtbtbtbtbtbtbtbtbtbtbtbtbtbtbtbtbtbtbtbtbtbtbtbtbtbtbtbtbtbtbtbtbtbtbtbtbtbtbtbtbtbtbtbtbtbtbtbtbtbtbtbtbtbtbtbtbtbtbtbtbtbtbtbtbtbtbtbtbtbtbtbtbGaZb7cab0#1#vfDfCepgqi4fAi2gogagagagagagagagagagafei3i2fQgmfvemfLf##LelekctQtQtQtQtQtQtQtQtQtQtQtQtQtQtQtQtQtQtQtQtQtQtQtQt",
"QtQtQtQtQtQtQtQtQtQtQtQtQtQtQtQtQtQtQtQtQtQtQtQtctekel#Lf#fLemfvgef3gffBggfefefefefefefefefefeghgffdeWi1epfCfD#v#1b0cab7aZbGbtbtbtbtbtbtbtbtbtbtbtbtbtbtbtbtbtbtbtbtbtbtbtbtbtbtbtbtbtbtbtbtbtbtbtbtbtbtbtbtbtbtbtbtbtbtbtbtbtbtbtbtbtbtbtbtbtbtbtbtbtbtbtbtbtbtbtbtbtbtbtbtbtbtbtbtbtbtbtbtbtbtbtbtbtbtbtbtbtbtbtbtbtbtbtbtbtbtbtbtbtbtbtbtbtbtbtbtbtbtbtbtbtbtbtbtbtbtbtbtbtbtbtbtbtbtbtbtbtbtbtbtbGaZb7cab0#1#vfDfCepi1eWfdgfghfefefefefefefefefefeggfBgff3gefvemfLf##LelekctQtQtQtQtQtQtQtQtQtQtQtQtQtQtQtQtQtQtQtQtQtQtQtQt",
"QtQtQtQtQtQtQtQtQtQtQtQtQtQtQtQtQtQtQtQtQtQtQtQtctekel#LiPd7aKeJiQiRiSiTiUiViViViViViViViViViVfXiWgGiXiYiZfLi0#v#1b0cab7aZbGbtbtbtbtbtbtbtbtbtbtbtbtbtbtbtbtbtbtbtbtbtbtbtbtbtbtbtbtbtbtbtbtbtbtbtbtbtbtbtbtbtbtbtbtbtbtbtbtbtbtbtbtbtbtbtbtbtbtbtbtbtbtbtbtbtbtbtbtbtbtbtbtbtbtbtbtbtbtbtbtbtbtbtbtbtbtbtbtbtbtbtbtbtbtbtbtbtbtbtbtbtbtbtbtbtbtbtbtbtbtbtbtbtbtbtbtbtbtbtbtbtbtbtbtbtbtbtbtbtbtbtbtbGaZb7cab0#1#vi0fLiZiYiXgGiWfXiViViViViViViViViViViUiTiSiRiQeJaKd7iP#LelekctQtQtQtQtQtQtQtQtQtQtQtQtQtQtQtQtQtQtQtQtQtQtQtQt",
"QtQtQtQtQtQtQtQtQtQtQtQtQtQtQtQtQtQtQtQtQtQtQtQtctekel.Zbod6aziEiFiGiHiIiJiJiJiJiJiJiJiJiJiJiJiKiLiMiNiAendOiO#u#1b0cab7aZbGbtbtbtbtbtbtbtbtbtbtbtbtbtbtbtbtbtbtbtbtbtbtbtbtbtbtbtbtbtbtbtbtbtbtbtbtbtbtbtbtbtbtbtbtbtbtbtbtbtbtbtbtbtbtbtbtbtbtbtbtbtbtbtbtbtbtbtbtbtbtbtbtbtbtbtbtbtbtbtbtbtbtbtbtbtbtbtbtbtbtbtbtbtbtbtbtbtbtbtbtbtbtbtbtbtbtbtbtbtbtbtbtbtbtbtbtbtbtbtbtbtbtbtbtbtbtbtbtbtbtbtbtbGaZb7cab0#1#uiOdOeniAiNiMiLiKiJiJiJiJiJiJiJiJiJiJiJiIiHiGiFiEazd6bo.ZelekctQtQtQtQtQtQtQtQtQtQtQtQtQtQtQtQtQtQtQtQtQtQtQtQt",
"QtQtQtQtQtQtQtQtQtQtQtQtQtQtQtQtQtQtQtQtQtQtQtQtctekel.ZbUdMdLiwgRixiyiziAiAiAiAiAiAiAiAiAiAiAiBiyiCg8iDazbohc#u#1b0cab7aZbGbtbtbtbtbtbtbtbtbtbtbtbtbtbtbtbtbtbtbtbtbtbtbtbtbtbtbtbtbtbtbtbtbtbtbtbtbtbtbtbtbtbtbtbtbtbtbtbtbtbtbtbtbtbtbtbtbtbtbtbtbtbtbtbtbtbtbtbtbtbtbtbtbtbtbtbtbtbtbtbtbtbtbtbtbtbtbtbtbtbtbtbtbtbtbtbtbtbtbtbtbtbtbtbtbtbtbtbtbtbtbtbtbtbtbtbtbtbtbtbtbtbtbtbtbtbtbtbtbtbtbtbtbGaZb7cab0#1#uhcboaziDg8iCiyiBiAiAiAiAiAiAiAiAiAiAiAiziyixgRiwdLdMbU.ZelekctQtQtQtQtQtQtQtQtQtQtQtQtQtQtQtQtQtQtQtQtQtQtQtQt",
"QtQtQtQtQtQtQtQtQtQtQtQtQtQtQtQtQtQtQtQtQtQtQtQtctekhj.Z.Z.Z.Z#LbUbUererererererererererererererererbU.Y.Z#MbJbn#1b0cab7aZbGbtbtbtbtbtbtbtbtbtbtbtbtbtbtbtbtbtbtbtbtbtbtbtbtbtbtbtbtbtbtbtbtbtbtbtbtbtbtbtbtbtbtbtbtbtbtbtbtbtbtbtbtbtbtbtbtbtbtbtbtbtbtbtbtbtbtbtbtbtbtbtbtbtbtbtbtbtbtbtbtbtbtbtbtbtbtbtbtbtbtbtbtbtbtbtbtbtbtbtbtbtbtbtbtbtbtbtbtbtbtbtbtbtbtbtbtbtbtbtbtbtbtbtbtbtbtbtbtbtbtbtbtbGaZb7cab0#1bnbJ#M.Z.YbUererererererererererererererererbUbU#L.Z.Z.Z.ZhjekctQtQtQtQtQtQtQtQtQtQtQtQtQtQtQtQtQtQtQtQtQtQtQtQt",
"QtQtQtQtQtQtQtQtQtQtQtQtQtQtQtQtQtQtQtQtQtQtQtQtd3iuiv.Z.ZeA.ZdMf#d8fufLd8d8d8d8d8d8d8d8d8d8d8fLfufLdObo#LdudQbn#1b0cab7aZbGbtbtbtbtbtbtbtbtbtbtbtbtbtbtbtbtbtbtbtbtbtbtbtbtbtbtbtbtbtbtbtbtbtbtbtbtbtbtbtbtbtbtbtbtbtbtbtbtbtbtbtbtbtbtbtbtbtbtbtbtbtbtbtbtbtbtbtbtbtbtbtbtbtbtbtbtbtbtbtbtbtbtbtbtbtbtbtbtbtbtbtbtbtbtbtbtbtbtbtbtbtbtbtbtbtbtbtbtbtbtbtbtbtbtbtbtbtbtbtbtbtbtbtbtbtbtbtbtbtbtbtbtbGaZb7cab0#1bndQdu#LbodOfLfufLd8d8d8d8d8d8d8d8d8d8d8fLfud8f#dM.ZeA.Z.Ziviud3QtQtQtQtQtQtQtQtQtQtQtQtQtQtQtQtQtQtQtQtQtQtQtQt",
"QtQtQtQtQtQtQtQtQtQtQtQtQtQtQtQtQtQtQtQtQtQtQtQtdrhtc8.Z.Z.Z.ZbUe.eLdNdNdNeLeLeLeLeLeLeLeLeLeLdNdNdNboer.ZdudQbn#1b0cab7aZbGbtbtbtbtbtbtbtbtbtbtbtbtbtbtbtbtbtbtbtbtbtbtbtbtbtbtbtbtbtbtbtbtbtbtbtbtbtbtbtbtbtbtbtbtbtbtbtbtbtbtbtbtbtbtbtbtbtbtbtbtbtbtbtbtbtbtbtbtbtbtbtbtbtbtbtbtbtbtbtbtbtbtbtbtbtbtbtbtbtbtbtbtbtbtbtbtbtbtbtbtbtbtbtbtbtbtbtbtbtbtbtbtbtbtbtbtbtbtbtbtbtbtbtbtbtbtbtbtbtbtbtbtbGaZb7cab0#1bndQdu.ZerbodNdNdNeLeLeLeLeLeLeLeLeLeLdNdNdNeLe.bU.Z.Z.Z.Zc8htdrQtQtQtQtQtQtQtQtQtQtQtQtQtQtQtQtQtQtQtQtQtQtQtQt",
"QtQtQtQtQtQtQtQtQtQtQtQtQtQtQtQtQtQtQtQtQtQtQtQtd3itd5.Z.Z.Z.Z.Z.Z.Z.Z.Z.Z.Z.Z.Z.Z.Z.Z.Z.Z.Z.Z.Z.Z.Z.Z.Z.ZbUbJ#u#1b0cab7aZbGbtbtbtbtbtbtbtbtbtbtbtbtbtbtbtbtbtbtbtbtbtbtbtbtbtbtbtbtbtbtbtbtbtbtbtbtbtbtbtbtbtbtbtbtbtbtbtbtbtbtbtbtbtbtbtbtbtbtbtbtbtbtbtbtbtbtbtbtbtbtbtbtbtbtbtbtbtbtbtbtbtbtbtbtbtbtbtbtbtbtbtbtbtbtbtbtbtbtbtbtbtbtbtbtbtbtbtbtbtbtbtbtbtbtbtbtbtbtbtbtbtbtbtbtbtbtbtbtbtbtbtbtbGaZb7cab0#1#ubJbU.Z.Z.Z.Z.Z.Z.Z.Z.Z.Z.Z.Z.Z.Z.Z.Z.Z.Z.Z.Z.Z.Z.Z.Z.Z.Zd5itd3QtQtQtQtQtQtQtQtQtQtQtQtQtQtQtQtQtQtQtQtQtQtQtQt",
"QtQtQtQtQtQtQtQtQtQtQtQtQtQtQtQtQtQtQtQtQtQtQtQtiliminiohzip.H.H.H.H.H.H.H.H.H.H.H.H.H.H.H.H.Hiqir.G#HishA#MbJbn#1b0cab7aZbGbtbtbtbtbtbtbtbtbtbtbtbtbtbtbtbtbtbtbtbtbtbtbtbtbtbtbtbtbtbtbtbtbtbtbtbtbtbtbtbtbtbtbtbtbtbtbtbtbtbtbtbtbtbtbtbtbtbtbtbtbtbtbtbtbtbtbtbtbtbtbtbtbtbtbtbtbtbtbtbtbtbtbtbtbtbtbtbtbtbtbtbtbtbtbtbtbtbtbtbtbtbtbtbtbtbtbtbtbtbtbtbtbtbtbtbtbtbtbtbtbtbtbtbtbtbtbtbtbtbtbtbtbGaZb7cab0#1bnbJ#MhAis#H.Giriq.H.H.H.H.H.H.H.H.H.H.H.H.H.H.H.H.HiphzioinimilQtQtQtQtQtQtQtQtQtQtQtQtQtQtQtQtQtQtQtQtQtQtQtQt",
"QtQtQtQtQtQtQtQtQtQtQtQtQtQtQtQtQtQtQtQtQtQtQtQt.hcrhHif.Lig.s.s.s.s.s.s.s.s.s.s.s.s.s.s.s.s.sih.oiiij.Hik#M#ubn#1b0cab7aZbGbtbtbtbtbtbtbtbtbtbtbtbtbtbtbtbtbtbtbtbtbtbtbtbtbtbtbtbtbtbtbtbtbtbtbtbtbtbtbtbtbtbtbtbtbtbtbtbtbtbtbtbtbtbtbtbtbtbtbtbtbtbtbtbtbtbtbtbtbtbtbtbtbtbtbtbtbtbtbtbtbtbtbtbtbtbtbtbtbtbtbtbtbtbtbtbtbtbtbtbtbtbtbtbtbtbtbtbtbtbtbtbtbtbtbtbtbtbtbtbtbtbtbtbtbtbtbtbtbtbtbtbtbGaZb7cab0#1bn#u#Mik.Hijii.oih.s.s.s.s.s.s.s.s.s.s.s.s.s.s.s.s.sig.LifhHcr.hQtQtQtQtQtQtQtQtQtQtQtQtQtQtQtQtQtQtQtQtQtQtQtQt",
"QtQtQtQtQtQtQtQtQtQtQtQtQtQtQtQtQtQtQtQtQtQtQtQt.#ib.eicicic.g.g.g.g.g.g.g.g.g.g.g.g.g.g.g.g.gidQt.dhViec.#M#ubn#1b0cab7aZbGbtbtbtbtbtbtbtbtbtbtbtbtbtbtbtbtbtbtbtbtbtbtbtbtbtbtbtbtbtbtbtbtbtbtbtbtbtbtbtbtbtbtbtbtbtbtbtbtbtbtbtbtbtbtbtbtbtbtbtbtbtbtbtbtbtbtbtbtbtbtbtbtbtbtbtbtbtbtbtbtbtbtbtbtbtbtbtbtbtbtbtbtbtbtbtbtbtbtbtbtbtbtbtbtbtbtbtbtbtbtbtbtbtbtbtbtbtbtbtbtbtbtbtbtbtbtbtbtbtbtbtbtbGaZb7cab0#1bn#u#Mc.iehV.dQtid.g.g.g.g.g.g.g.g.g.g.g.g.g.g.g.g.gicicic.eib.#QtQtQtQtQtQtQtQtQtQtQtQtQtQtQtQtQtQtQtQtQtQtQtQt",
"QtQtQtQtQtQtQtQtQtQtQtQtQtQtQtQtQtQtQtQtQtQt.j.jQtQtQtQtQtQtQtQtQtQtQtQtQtQtQtQtQtQtQtQtQtQtQtQtQtQtcgiabZ#M#ubn#1b0cab7aZbGbtbtbtbtbtbtbtbtbtbtbtbtbtbtbtbtbtbtbtbtbtbtbtbtbtbtbtbtbtbtbtbtbtbtbtbtbtbtbtbtbtbtbtbtbtbtbtbtbtbtbtbtbtbtbtbtbtbtbtbtbtbtbtbtbtbtbtbtbtbtbtbtbtbtbtbtbtbtbtbtbtbtbtbtbtbtbtbtbtbtbtbtbtbtbtbtbtbtbtbtbtbtbtbtbtbtbtbtbtbtbtbtbtbtbtbtbtbtbtbtbtbtbtbtbtbtbtbtbtbtbtbtbGaZb7cab0#1bn#u#MbZiacgQtQtQtQtQtQtQtQtQtQtQtQtQtQtQtQtQtQtQtQtQtQtQtQtQtQt.j.jQtQtQtQtQtQtQtQtQtQtQtQtQtQtQtQtQtQtQtQtQtQt",
"QtQtQtQtQtQtQtQtQtQtQtQtQtQtQtQtQtQtQtQtQtQt.j.jQtQtQtQtQtQtQtQtQtQtQtQtQtQtQtQtQtQtQtQtQtQtQtQtQtQti#iabZ#M#ubn#1b0cab7aZbGbtbtbtbtbtbtbtbtbtbtbtbtbtbtbtbtbtbtbtbtbtbtbtbtbtbtbtbtbtbtbtbtbtbtbtbtbtbtbtbtbtbtbtbtbtbtbtbtbtbtbtbtbtbtbtbtbtbtbtbtbtbtbtbtbtbtbtbtbtbtbtbtbtbtbtbtbtbtbtbtbtbtbtbtbtbtbtbtbtbtbtbtbtbtbtbtbtbtbtbtbtbtbtbtbtbtbtbtbtbtbtbtbtbtbtbtbtbtbtbtbtbtbtbtbtbtbtbtbtbtbtbtbGaZb7cab0#1bn#u#MbZiai#QtQtQtQtQtQtQtQtQtQtQtQtQtQtQtQtQtQtQtQtQtQtQtQtQtQt.j.jQtQtQtQtQtQtQtQtQtQtQtQtQtQtQtQtQtQtQtQtQtQt",
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
"QtQtQtQtQtQtQtQtQtQtQtQtQtQtQtQtQtQtQtQtQtQtQtQta.cqhRhShThHhUhUhUhUhUhUhUhUhUhUhUhUhUhUhUhUhUhVhWhXd4hYhZ#M#ubn#1b0cab7aZbGbtbtbtbtbtbtbtbtbtbtbtbtbtbtbtbtbtbtbtbtbtbtbtbtbtbtbtbtbtbtbtbtbtbtbtbtbtbtbtbtbtbtbtbtbtbtbtbtbtbtbtbtbtbtbtbtbtbtbtbtbtbtbtbtbtbtbtbtbtbtbtbtbtbtbtbtbtbtbtbtbtbtbtbtbtbtbtbtbtbtbtbtbtbtbtbtbtbtbtbtbtbtbtbtbtbtbtbtbtbtbtbtbtbtbtbtbtbtbtbtbtbtbtbtbtbtbtbtbtbtbtbtbGaZb7cab0#1bn#u#MhZhYd4hXhWhVhUhUhUhUhUhUhUhUhUhUhUhUhUhUhUhUhUhHhThShRcqa.QtQtQtQtQtQtQtQtQtQtQtQtQtQtQtQtQtQtQtQtQtQtQtQt",
"QtQtQtQtQtQtQtQtQtQtQtQtQtQtQtQtQtQtQtQtQtQtQtQtcphHhIhJhKhLhMhMhMhMhMhMhMhMhMhMhMhMhMhMhMhMhMhN#WhO.Hd.hB#MbJbn#1b0cab7aZbGbtbtbtbtbtbtbtbtbtbtbtbtbtbtbtbtbtbtbtbtbtbtbtbtbtbtbtbtbtbtbtbtbtbtbtbtbtbtbtbtbtbtbtbtbtbtbtbtbtbtbtbtbtbtbtbtbtbtbtbtbtbtbtbtbtbtbtbtbtbtbtbtbtbtbtbtbtbtbtbtbtbtbtbtbtbtbtbtbtbtbtbtbtbtbtbtbtbtbtbtbtbtbtbtbtbtbtbtbtbtbtbtbtbtbtbtbtbtbtbtbtbtbtbtbtbtbtbtbtbtbtbtbGaZb7cab0#1bnbJ#MhBd..HhO#WhNhMhMhMhMhMhMhMhMhMhMhMhMhMhMhMhMhMhLhKhJhIhHcpQtQtQtQtQtQtQtQtQtQtQtQtQtQtQtQtQtQtQtQtQtQtQtQt",
"QtQtQtQtQtQtQtQtQtQtQtQtQtQtQtQtQtQtQtQtQtQtQtQtcthyhz.Z.Z.ZhAhAhAhAhAhAhAhAhAhAhAhAhAhAhAhAhAhBhBhAhCda.ZbUbJ#u#1b0cab7aZbGbtbtbtbtbtbtbtbtbtbtbtbtbtbtbtbtbtbtbtbtbtbtbtbtbtbtbtbtbtbtbtbtbtbtbtbtbtbtbtbtbtbtbtbtbtbtbtbtbtbtbtbtbtbtbtbtbtbtbtbtbtbtbtbtbtbtbtbtbtbtbtbtbtbtbtbtbtbtbtbtbtbtbtbtbtbtbtbtbtbtbtbtbtbtbtbtbtbtbtbtbtbtbtbtbtbtbtbtbtbtbtbtbtbtbtbtbtbtbtbtbtbtbtbtbtbtbtbtbtbtbtbtbGaZb7cab0#1#ubJbU.ZdahChAhBhBhAhAhAhAhAhAhAhAhAhAhAhAhAhAhAhAhA.Z.Z.ZhzhyctQtQtQtQtQtQtQtQtQtQtQtQtQtQtQtQtQtQtQtQtQtQtQtQt",
"QtQtQtQtQtQtQtQtQtQtQtQtQtQtQtQtQtQtQtQtQtQtQtQtdrhtc8.Z.Z.Z.Z.YdMe.boboe.e.e.e.e.e.e.e.e.e.e.boboe.dMbU.ZdudQbn#1b0cab7aZbGbtbtbtbtbtbtbtbtbtbtbtbtbtbtbtbtbtbtbtbtbtbtbtbtbtbtbtbtbtbtbtbtbtbtbtbtbtbtbtbtbtbtbtbtbtbtbtbtbtbtbtbtbtbtbtbtbtbtbtbtbtbtbtbtbtbtbtbtbtbtbtbtbtbtbtbtbtbtbtbtbtbtbtbtbtbtbtbtbtbtbtbtbtbtbtbtbtbtbtbtbtbtbtbtbtbtbtbtbtbtbtbtbtbtbtbtbtbtbtbtbtbtbtbtbtbtbtbtbtbtbtbtbGaZb7cab0#1bndQdu.ZbUdMe.boboe.e.e.e.e.e.e.e.e.e.e.boboe.dM.Y.Z.Z.Z.Zc8htdrQtQtQtQtQtQtQtQtQtQtQtQtQtQtQtQtQtQtQtQtQtQtQtQt",
"QtQtQtQtQtQtQtQtQtQtQtQtQtQtQtQtQtQtQtQtQtQtQtQtdrhohp.Z.ZeA.ZdMf#d7fLd8d7d7d7d7d7d7d7d7d7d7d7d8fLd8d9e.#LdudQbn#1b0cab7aZbGbtbtbtbtbtbtbtbtbtbtbtbtbtbtbtbtbtbtbtbtbtbtbtbtbtbtbtbtbtbtbtbtbtbtbtbtbtbtbtbtbtbtbtbtbtbtbtbtbtbtbtbtbtbtbtbtbtbtbtbtbtbtbtbtbtbtbtbtbtbtbtbtbtbtbtbtbtbtbtbtbtbtbtbtbtbtbtbtbtbtbtbtbtbtbtbtbtbtbtbtbtbtbtbtbtbtbtbtbtbtbtbtbtbtbtbtbtbtbtbtbtbtbtbtbtbtbtbtbtbtbtbtbGaZb7cab0#1bndQdu#Le.d9d8fLd8d7d7d7d7d7d7d7d7d7d7d7d8fLd7f#dM.ZeA.Z.ZhphodrQtQtQtQtQtQtQtQtQtQtQtQtQtQtQtQtQtQtQtQtQtQtQtQt",
"QtQtQtQtQtQtQtQtQtQtQtQtQtQtQtQtQtQtQtQtQtQtQtQtctekhj.Z.Z.Z.ZbUe.dNdNdNdNdNdNdNdNdNdNdNdNdNdNdNdNdNboer.Z#M#ubn#1b0cab7aZbGbtbtbtbtbtbtbtbtbtbtbtbtbtbtbtbtbtbtbtbtbtbtbtbtbtbtbtbtbtbtbtbtbtbtbtbtbtbtbtbtbtbtbtbtbtbtbtbtbtbtbtbtbtbtbtbtbtbtbtbtbtbtbtbtbtbtbtbtbtbtbtbtbtbtbtbtbtbtbtbtbtbtbtbtbtbtbtbtbtbtbtbtbtbtbtbtbtbtbtbtbtbtbtbtbtbtbtbtbtbtbtbtbtbtbtbtbtbtbtbtbtbtbtbtbtbtbtbtbtbtbtbtbGaZb7cab0#1bn#u#M.ZerbodNdNdNdNdNdNdNdNdNdNdNdNdNdNdNdNdNe.bU.Z.Z.Z.ZhjekctQtQtQtQtQtQtQtQtQtQtQtQtQtQtQtQtQtQtQtQtQtQtQtQt",
"QtQtQtQtQtQtQtQtQtQtQtQtQtQtQtQtQtQtQtQtQtQtQtQtctekel.Z.YbU.ZgKg5g6g7g8g9g9g9g9g9g9g9g9g9g9g9h.g7h#hahbaz#ehc#u#1b0cab7aZbGbtbtbtbtbtbtbtbtbtbtbtbtbtbtbtbtbtbtbtbtbtbtbtbtbtbtbtbtbtbtbtbtbtbtbtbtbtbtbtbtbtbtbtbtbtbtbtbtbtbtbtbtbtbtbtbtbtbtbtbtbtbtbtbtbtbtbtbtbtbtbtbtbtbtbtbtbtbtbtbtbtbtbtbtbtbtbtbtbtbtbtbtbtbtbtbtbtbtbtbtbtbtbtbtbtbtbtbtbtbtbtbtbtbtbtbtbtbtbtbtbtbtbtbtbtbtbtbtbtbtbtbtbGaZb7cab0#1#uhc#eazhbhah#g7h.g9g9g9g9g9g9g9g9g9g9g9g8g7g6g5gK.ZbU.Y.ZelekctQtQtQtQtQtQtQtQtQtQtQtQtQtQtQtQtQtQtQtQtQtQtQtQt",
"QtQtQtQtQtQtQtQtQtQtQtQtQtQtQtQtQtQtQtQtQtQtQtQtctekel.Ze.dN#YgReDgSgTgUgVgVgVgVgVgVgVgVgVgVgVgWgTgXeEgYgZf#g0#u#1b0cab7aZbGbtbtbtbtbtbtbtbtbtbtbtbtbtbtbtbtbtbtbtbtbtbtbtbtbtbtbtbtbtbtbtbtbtbtbtbtbtbtbtbtbtbtbtbtbtbtbtbtbtbtbtbtbtbtbtbtbtbtbtbtbtbtbtbtbtbtbtbtbtbtbtbtbtbtbtbtbtbtbtbtbtbtbtbtbtbtbtbtbtbtbtbtbtbtbtbtbtbtbtbtbtbtbtbtbtbtbtbtbtbtbtbtbtbtbtbtbtbtbtbtbtbtbtbtbtbtbtbtbtbtbtbtbGaZb7cab0#1#ug0f#gZgYeEgXgTgWgVgVgVgVgVgVgVgVgVgVgVgUgTgSeDgR#YdNe..ZelekctQtQtQtQtQtQtQtQtQtQtQtQtQtQtQtQtQtQtQtQtQtQtQtQt",
"QtQtQtQtQtQtQtQtQtQtQtQtQtQtQtQtQtQtQtQtQtQtQtQtctekel#LdNgwaKgxgygzgAgBgCgDgDgDgDgDgDgDgDgDgEgFgGgHgIgJgKd8gL#v#1b0cab7aZbGbtbtbtbtbtbtbtbtbtbtbtbtbtbtbtbtbtbtbtbtbtbtbtbtbtbtbtbtbtbtbtbtbtbtbtbtbtbtbtbtbtbtbtbtbtbtbtbtbtbtbtbtbtbtbtbtbtbtbtbtbtbtbtbtbtbtbtbtbtbtbtbtbtbtbtbtbtbtbtbtbtbtbtbtbtbtbtbtbtbtbtbtbtbtbtbtbtbtbtbtbtbtbtbtbtbtbtbtbtbtbtbtbtbtbtbtbtbtbtbtbtbtbtbtbtbtbtbtbtbtbtbtbGaZb7cab0#1#vgLd8gKgJgIgHgGgFgEgDgDgDgDgDgDgDgDgDgCgBgAgzgygxaKgwdN#LelekctQtQtQtQtQtQtQtQtQtQtQtQtQtQtQtQtQtQtQtQtQtQtQtQt",
"QtQtQtQtQtQtQtQtQtQtQtQtQtQtQtQtQtQtQtQtQtQtQtQtctekel#Lf#fLemfvgmfQgnghgafhfhfhfhfhfhfhfhfhgagogngggpgqepfCfD#v#1b0cab7aZbGbtbtbtbtbtbtbtbtbtbtbtbtbtbtbtbtbtbtbtbtbtbtbtbtbtbtbtbtbtbtbtbtbtbtbtbtbtbtbtbtbtbtbtbtbtbtbtbtbtbtbtbtbtbtbtbtbtbtbtbtbtbtbtbtbtbtbtbtbtbtbtbtbtbtbtbtbtbtbtbtbtbtbtbtbtbtbtbtbtbtbtbtbtbtbtbtbtbtbtbtbtbtbtbtbtbtbtbtbtbtbtbtbtbtbtbtbtbtbtbtbtbtbtbtbtbtbtbtbtbtbtbtbGaZb7cab0#1#vfDfCepgqgpgggngogafhfhfhfhfhfhfhfhfhgaghgnfQgmfvemfLf##LelekctQtQtQtQtQtQtQtQtQtQtQtQtQtQtQtQtQtQtQtQtQtQtQtQt",
"QtQtQtQtQtQtQtQtQtQtQtQtQtQtQtQtQtQtQtQtQtQtQtQtctekel#Lf#fLemfvgef3gffBggfefefefefefefefefefeghgfgieWgjepfCfD#v#1b0cab7aZbGbtbtbtbtbtbtbtbtbtbtbtbtbtbtbtbtbtbtbtbtbtbtbtbtbtbtbtbtbtbtbtbtbtbtbtbtbtbtbtbtbtbtbtbtbtbtbtbtbtbtbtbtbtbtbtbtbtbtbtbtbtbtbtbtbtbtbtbtbtbtbtbtbtbtbtbtbtbtbtbtbtbtbtbtbtbtbtbtbtbtbtbtbtbtbtbtbtbtbtbtbtbtbtbtbtbtbtbtbtbtbtbtbtbtbtbtbtbtbtbtbtbtbtbtbtbtbtbtbtbtbtbtbGaZb7cab0#1#vfDfCepgjeWgigfghfefefefefefefefefefeggfBgff3gefvemfLf##LelekctQtQtQtQtQtQtQtQtQtQtQtQtQtQtQtQtQtQtQtQtQtQtQtQt",
"QtQtQtQtQtQtQtQtQtQtQtQtQtQtQtQtQtQtQtQtQtQtQtQtctekel#Lf#d8emfafbfcg#feffffffffffffffffffffffgag#gbe2gceofkfl#v#1b0cab7aZbGbtbtbtbtbtbtbtbtbtbtbtbtbtbtbtbtbtbtbtbtbtbtbtbtbtbtbtbtbtbtbtbtbtbtbtbtbtbtbtbtbtbtbtbtbtbtbtbtbtbtbtbtbtbtbtbtbtbtbtbtbtbtbtbtbtbtbtbtbtbtbtbtbtbtbtbtbtbtbtbtbtbtbtbtbtbtbtbtbtbtbtbtbtbtbtbtbtbtbtbtbtbtbtbtbtbtbtbtbtbtbtbtbtbtbtbtbtbtbtbtbtbtbtbtbtbtbtbtbtbtbtbtbGaZb7cab0#1#vflfkeogce2gbg#gafffffffffffffffffffffffeg#fcfbfaemd8f##LelekctQtQtQtQtQtQtQtQtQtQtQtQtQtQtQtQtQtQtQtQtQtQtQtQt",
"QtQtQtQtQtQtQtQtQtQtQtQtQtQtQtQtQtQtQtQtQtQtQtQtctekel#Lf#d8emfVfWfXfAf3dxfcfcfcfcfcfcfcfcfcfcfQfAfgeZeHeofkfl#v#1b0cab7aZbGbtbtbtbtbtbtbtbtbtbtbtbtbtbtbtbtbtbtbtbtbtbtbtbtbtbtbtbtbtbtbtbtbtbtbtbtbtbtbtbtbtbtbtbtbtbtbtbtbtbtbtbtbtbtbtbtbtbtbtbtbtbtbtbtbtbtbtbtbtbtbtbtbtbtbtbtbtbtbtbtbtbtbtbtbtbtbtbtbtbtbtbtbtbtbtbtbtbtbtbtbtbtbtbtbtbtbtbtbtbtbtbtbtbtbtbtbtbtbtbtbtbtbtbtbtbtbtbtbtbtbtbtbGaZb7cab0#1#vflfkeoeHeZfgfAfQfcfcfcfcfcfcfcfcfcfcdxf3fAfXfWfVemd8f##LelekctQtQtQtQtQtQtQtQtQtQtQtQtQtQtQtQtQtQtQtQtQtQtQtQt",
"QtQtQtQtQtQtQtQtQtQtQtQtQtQtQtQtQtQtQtQtQtQtQtQtctekel#Lf#d8emfVfWfXfAf3dxfcfcfcfcfcfcfcfcfcfcfQfAfgeZeHeofkfl#v#1b0cab7aZbGbtbtbtbtbtbtbtbtbtbtbtbtbtbtbtbtbtbtbtbtbtbtbtbtbtbtbtbtbtbtbtbtbtbtbtbtbtbtbtbtbtbtbtbtbtbtbtbtbtbtbtbtbtbtbtbtbtbtbtbtbtbtbtbtbtbtbtbtbtbtbtbtbtbtbtbtbtbtbtbtbtbtbtbtbtbtbtbtbtbtbtbtbtbtbtbtbtbtbtbtbtbtbtbtbtbtbtbtbtbtbtbtbtbtbtbtbtbtbtbtbtbtbtbtbtbtbtbtbtbtbtbtbGaZb7cab0#1#vflfkeoeHeZfgfAfQfcfcfcfcfcfcfcfcfcfcdxf3fAfXfWfVemd8f##LelekctQtQtQtQtQtQtQtQtQtQtQtQtQtQtQtQtQtQtQtQtQtQtQtQt",
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
